tootap/Track-on-track/firmware/msp430fr6989.h

/* ============================================================================ */
/* Copyright (c) 2017, Texas Instruments Incorporated                           */
/*  All rights reserved.                                                        */
/*                                                                              */
/*  Redistribution and use in source and binary forms, with or without          */
/*  modification, are permitted provided that the following conditions          */
/*  are met:                                                                    */
/*                                                                              */
/*  *  Redistributions of source code must retain the above copyright           */
/*     notice, this list of conditions and the following disclaimer.            */
/*                                                                              */
/*  *  Redistributions in binary form must reproduce the above copyright        */
/*     notice, this list of conditions and the following disclaimer in the      */
/*     documentation and/or other materials provided with the distribution.     */
/*                                                                              */
/*  *  Neither the name of Texas Instruments Incorporated nor the names of      */
/*     its contributors may be used to endorse or promote products derived      */
/*     from this software without specific prior written permission.            */
/*                                                                              */
/*  THIS SOFTWARE IS PROVIDED BY THE COPYRIGHT HOLDERS AND CONTRIBUTORS "AS IS" */
/*  AND ANY EXPRESS OR IMPLIED WARRANTIES, INCLUDING, BUT NOT LIMITED TO,       */
/*  THE IMPLIED WARRANTIES OF MERCHANTABILITY AND FITNESS FOR A PARTICULAR      */
/*  PURPOSE ARE DISCLAIMED. IN NO EVENT SHALL THE COPYRIGHT OWNER OR            */
/*  CONTRIBUTORS BE LIABLE FOR ANY DIRECT, INDIRECT, INCIDENTAL, SPECIAL,       */
/*  EXEMPLARY, OR CONSEQUENTIAL DAMAGES (INCLUDING, BUT NOT LIMITED TO,         */
/*  PROCUREMENT OF SUBSTITUTE GOODS OR SERVICES; LOSS OF USE, DATA, OR PROFITS; */
/*  OR BUSINESS INTERRUPTION) HOWEVER CAUSED AND ON ANY THEORY OF LIABILITY,    */
/*  WHETHER IN CONTRACT, STRICT LIABILITY, OR TORT (INCLUDING NEGLIGENCE OR     */
/*  OTHERWISE) ARISING IN ANY WAY OUT OF THE USE OF THIS SOFTWARE,              */
/*  EVEN IF ADVISED OF THE POSSIBILITY OF SUCH DAMAGE.                          */
/* ============================================================================ */

/********************************************************************
*
* Standard register and bit definitions for the Texas Instruments
* MSP430 microcontroller.
*
* This file supports assembler and C development for
* MSP430FR6989 devices.
*
* Texas Instruments, Version 1.1
*
* Rev. 1.0, Setup
* Rev. 1.1, ESI: Renamed bit ESIVCC2 to ESIVMIDEN, renamed bit ESIVSS to ESISHTSM
*
*
********************************************************************/

#ifndef __MSP430FR6989
#define __MSP430FR6989

#define __MSP430_HAS_MSP430XV2_CPU__                /* Definition to show that it has MSP430XV2 CPU */
#define __MSP430FR5XX_6XX_FAMILY__

#define __MSP430_HEADER_VERSION__ 1203

#ifdef __cplusplus
extern "C" {
#endif


/*----------------------------------------------------------------------------*/
/* PERIPHERAL FILE MAP                                                        */
/*----------------------------------------------------------------------------*/

#ifndef SFR_8BIT
/* External references resolved by a device-specific linker command file */
#define SFR_8BIT(address)   extern volatile unsigned char address
#define SFR_16BIT(address)  extern volatile unsigned int address
//#define SFR_20BIT(address)  extern volatile unsigned int address
typedef void (* __SFR_FARPTR)();
#define SFR_20BIT(address) extern __SFR_FARPTR address
#define SFR_32BIT(address)  extern volatile unsigned long address

#endif


/************************************************************
* STANDARD BITS
************************************************************/

#define BIT0                   (0x0001)
#define BIT1                   (0x0002)
#define BIT2                   (0x0004)
#define BIT3                   (0x0008)
#define BIT4                   (0x0010)
#define BIT5                   (0x0020)
#define BIT6                   (0x0040)
#define BIT7                   (0x0080)
#define BIT8                   (0x0100)
#define BIT9                   (0x0200)
#define BITA                   (0x0400)
#define BITB                   (0x0800)
#define BITC                   (0x1000)
#define BITD                   (0x2000)
#define BITE                   (0x4000)
#define BITF                   (0x8000)

/************************************************************
* STATUS REGISTER BITS
************************************************************/

#define C                      (0x0001)
#define Z                      (0x0002)
#define N                      (0x0004)
#define V                      (0x0100)
#define GIE                    (0x0008)
#define CPUOFF                 (0x0010)
#define OSCOFF                 (0x0020)
#define SCG0                   (0x0040)
#define SCG1                   (0x0080)

/* Low Power Modes coded with Bits 4-7 in SR */

#ifdef __ASM_HEADER__ /* Begin #defines for assembler */
#define LPM0                   (CPUOFF)
#define LPM1                   (SCG0+CPUOFF)
#define LPM2                   (SCG1+CPUOFF)
#define LPM3                   (SCG1+SCG0+CPUOFF)
#define LPM4                   (SCG1+SCG0+OSCOFF+CPUOFF)
/* End #defines for assembler */

#else /* Begin #defines for C */
#define LPM0_bits              (CPUOFF)
#define LPM1_bits              (SCG0+CPUOFF)
#define LPM2_bits              (SCG1+CPUOFF)
#define LPM3_bits              (SCG1+SCG0+CPUOFF)
#define LPM4_bits              (SCG1+SCG0+OSCOFF+CPUOFF)

#include "in430.h"
#include <intrinsics.h>

#define LPM0      __bis_SR_register(LPM0_bits)         /* Enter Low Power Mode 0 */
#define LPM0_EXIT __bic_SR_register_on_exit(LPM0_bits) /* Exit Low Power Mode 0 */
#define LPM1      __bis_SR_register(LPM1_bits)         /* Enter Low Power Mode 1 */
#define LPM1_EXIT __bic_SR_register_on_exit(LPM1_bits) /* Exit Low Power Mode 1 */
#define LPM2      __bis_SR_register(LPM2_bits)         /* Enter Low Power Mode 2 */
#define LPM2_EXIT __bic_SR_register_on_exit(LPM2_bits) /* Exit Low Power Mode 2 */
#define LPM3      __bis_SR_register(LPM3_bits)         /* Enter Low Power Mode 3 */
#define LPM3_EXIT __bic_SR_register_on_exit(LPM3_bits) /* Exit Low Power Mode 3 */
#define LPM4      __bis_SR_register(LPM4_bits)         /* Enter Low Power Mode 4 */
#define LPM4_EXIT __bic_SR_register_on_exit(LPM4_bits) /* Exit Low Power Mode 4 */
#endif /* End #defines for C */

/************************************************************
* PERIPHERAL FILE MAP
************************************************************/

/************************************************************
* ADC12_B
************************************************************/
#define __MSP430_HAS_ADC12_B__                /* Definition to show that Module is available */
#define __MSP430_BASEADDRESS_ADC12_B__ 0x0800
#define ADC12_B_BASE           __MSP430_BASEADDRESS_ADC12_B__

SFR_16BIT(ADC12CTL0);                         /* ADC12 B Control 0 */
SFR_8BIT(ADC12CTL0_L);                        /* ADC12 B Control 0 */
SFR_8BIT(ADC12CTL0_H);                        /* ADC12 B Control 0 */
SFR_16BIT(ADC12CTL1);                         /* ADC12 B Control 1 */
SFR_8BIT(ADC12CTL1_L);                        /* ADC12 B Control 1 */
SFR_8BIT(ADC12CTL1_H);                        /* ADC12 B Control 1 */
SFR_16BIT(ADC12CTL2);                         /* ADC12 B Control 2 */
SFR_8BIT(ADC12CTL2_L);                        /* ADC12 B Control 2 */
SFR_8BIT(ADC12CTL2_H);                        /* ADC12 B Control 2 */
SFR_16BIT(ADC12CTL3);                         /* ADC12 B Control 3 */
SFR_8BIT(ADC12CTL3_L);                        /* ADC12 B Control 3 */
SFR_8BIT(ADC12CTL3_H);                        /* ADC12 B Control 3 */
SFR_16BIT(ADC12LO);                           /* ADC12 B Window Comparator High Threshold */
SFR_8BIT(ADC12LO_L);                          /* ADC12 B Window Comparator High Threshold */
SFR_8BIT(ADC12LO_H);                          /* ADC12 B Window Comparator High Threshold */
SFR_16BIT(ADC12HI);                           /* ADC12 B Window Comparator High Threshold */
SFR_8BIT(ADC12HI_L);                          /* ADC12 B Window Comparator High Threshold */
SFR_8BIT(ADC12HI_H);                          /* ADC12 B Window Comparator High Threshold */
SFR_16BIT(ADC12IFGR0);                        /* ADC12 B Interrupt Flag 0 */
SFR_8BIT(ADC12IFGR0_L);                       /* ADC12 B Interrupt Flag 0 */
SFR_8BIT(ADC12IFGR0_H);                       /* ADC12 B Interrupt Flag 0 */
SFR_16BIT(ADC12IFGR1);                        /* ADC12 B Interrupt Flag 1 */
SFR_8BIT(ADC12IFGR1_L);                       /* ADC12 B Interrupt Flag 1 */
SFR_8BIT(ADC12IFGR1_H);                       /* ADC12 B Interrupt Flag 1 */
SFR_16BIT(ADC12IFGR2);                        /* ADC12 B Interrupt Flag 2 */
SFR_8BIT(ADC12IFGR2_L);                       /* ADC12 B Interrupt Flag 2 */
SFR_8BIT(ADC12IFGR2_H);                       /* ADC12 B Interrupt Flag 2 */
SFR_16BIT(ADC12IER0);                         /* ADC12 B Interrupt Enable 0 */
SFR_8BIT(ADC12IER0_L);                        /* ADC12 B Interrupt Enable 0 */
SFR_8BIT(ADC12IER0_H);                        /* ADC12 B Interrupt Enable 0 */
SFR_16BIT(ADC12IER1);                         /* ADC12 B Interrupt Enable 1 */
SFR_8BIT(ADC12IER1_L);                        /* ADC12 B Interrupt Enable 1 */
SFR_8BIT(ADC12IER1_H);                        /* ADC12 B Interrupt Enable 1 */
SFR_16BIT(ADC12IER2);                         /* ADC12 B Interrupt Enable 2 */
SFR_8BIT(ADC12IER2_L);                        /* ADC12 B Interrupt Enable 2 */
SFR_8BIT(ADC12IER2_H);                        /* ADC12 B Interrupt Enable 2 */
SFR_16BIT(ADC12IV);                           /* ADC12 B Interrupt Vector Word */
SFR_8BIT(ADC12IV_L);                          /* ADC12 B Interrupt Vector Word */
SFR_8BIT(ADC12IV_H);                          /* ADC12 B Interrupt Vector Word */

SFR_16BIT(ADC12MCTL0);                        /* ADC12 Memory Control 0 */
SFR_8BIT(ADC12MCTL0_L);                       /* ADC12 Memory Control 0 */
SFR_8BIT(ADC12MCTL0_H);                       /* ADC12 Memory Control 0 */
SFR_16BIT(ADC12MCTL1);                        /* ADC12 Memory Control 1 */
SFR_8BIT(ADC12MCTL1_L);                       /* ADC12 Memory Control 1 */
SFR_8BIT(ADC12MCTL1_H);                       /* ADC12 Memory Control 1 */
SFR_16BIT(ADC12MCTL2);                        /* ADC12 Memory Control 2 */
SFR_8BIT(ADC12MCTL2_L);                       /* ADC12 Memory Control 2 */
SFR_8BIT(ADC12MCTL2_H);                       /* ADC12 Memory Control 2 */
SFR_16BIT(ADC12MCTL3);                        /* ADC12 Memory Control 3 */
SFR_8BIT(ADC12MCTL3_L);                       /* ADC12 Memory Control 3 */
SFR_8BIT(ADC12MCTL3_H);                       /* ADC12 Memory Control 3 */
SFR_16BIT(ADC12MCTL4);                        /* ADC12 Memory Control 4 */
SFR_8BIT(ADC12MCTL4_L);                       /* ADC12 Memory Control 4 */
SFR_8BIT(ADC12MCTL4_H);                       /* ADC12 Memory Control 4 */
SFR_16BIT(ADC12MCTL5);                        /* ADC12 Memory Control 5 */
SFR_8BIT(ADC12MCTL5_L);                       /* ADC12 Memory Control 5 */
SFR_8BIT(ADC12MCTL5_H);                       /* ADC12 Memory Control 5 */
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
SFR_8BIT(ADC12MCTL24_H);                      /* ADC12 Memory Control 24 */
SFR_16BIT(ADC12MCTL25);                       /* ADC12 Memory Control 25 */
SFR_8BIT(ADC12MCTL25_L);                      /* ADC12 Memory Control 25 */
SFR_8BIT(ADC12MCTL25_H);                      /* ADC12 Memory Control 25 */
SFR_16BIT(ADC12MCTL26);                       /* ADC12 Memory Control 26 */
SFR_8BIT(ADC12MCTL26_L);                      /* ADC12 Memory Control 26 */
SFR_8BIT(ADC12MCTL26_H);                      /* ADC12 Memory Control 26 */
SFR_16BIT(ADC12MCTL27);                       /* ADC12 Memory Control 27 */
SFR_8BIT(ADC12MCTL27_L);                      /* ADC12 Memory Control 27 */
SFR_8BIT(ADC12MCTL27_H);                      /* ADC12 Memory Control 27 */
SFR_16BIT(ADC12MCTL28);                       /* ADC12 Memory Control 28 */
SFR_8BIT(ADC12MCTL28_L);                      /* ADC12 Memory Control 28 */
SFR_8BIT(ADC12MCTL28_H);                      /* ADC12 Memory Control 28 */
SFR_16BIT(ADC12MCTL29);                       /* ADC12 Memory Control 29 */
SFR_8BIT(ADC12MCTL29_L);                      /* ADC12 Memory Control 29 */
SFR_8BIT(ADC12MCTL29_H);                      /* ADC12 Memory Control 29 */
SFR_16BIT(ADC12MCTL30);                       /* ADC12 Memory Control 30 */
SFR_8BIT(ADC12MCTL30_L);                      /* ADC12 Memory Control 30 */
SFR_8BIT(ADC12MCTL30_H);                      /* ADC12 Memory Control 30 */
SFR_16BIT(ADC12MCTL31);                       /* ADC12 Memory Control 31 */
SFR_8BIT(ADC12MCTL31_L);                      /* ADC12 Memory Control 31 */
SFR_8BIT(ADC12MCTL31_H);                      /* ADC12 Memory Control 31 */
#define ADC12MCTL_             ADC12MCTL      /* ADC12 Memory Control */
#ifdef __ASM_HEADER__
#define ADC12MCTL              ADC12MCTL0     /* ADC12 Memory Control (for assembler) */
#else
#define ADC12MCTL              ((char*)       &ADC12MCTL0) /* ADC12 Memory Control (for C) */
#endif

SFR_16BIT(ADC12MEM0);                         /* ADC12 Conversion Memory 0 */
SFR_8BIT(ADC12MEM0_L);                        /* ADC12 Conversion Memory 0 */
SFR_8BIT(ADC12MEM0_H);                        /* ADC12 Conversion Memory 0 */
SFR_16BIT(ADC12MEM1);                         /* ADC12 Conversion Memory 1 */
SFR_8BIT(ADC12MEM1_L);                        /* ADC12 Conversion Memory 1 */
SFR_8BIT(ADC12MEM1_H);                        /* ADC12 Conversion Memory 1 */
SFR_16BIT(ADC12MEM2);                         /* ADC12 Conversion Memory 2 */
SFR_8BIT(ADC12MEM2_L);                        /* ADC12 Conversion Memory 2 */
SFR_8BIT(ADC12MEM2_H);                        /* ADC12 Conversion Memory 2 */
SFR_16BIT(ADC12MEM3);                         /* ADC12 Conversion Memory 3 */
SFR_8BIT(ADC12MEM3_L);                        /* ADC12 Conversion Memory 3 */
SFR_8BIT(ADC12MEM3_H);                        /* ADC12 Conversion Memory 3 */
SFR_16BIT(ADC12MEM4);                         /* ADC12 Conversion Memory 4 */
SFR_8BIT(ADC12MEM4_L);                        /* ADC12 Conversion Memory 4 */
SFR_8BIT(ADC12MEM4_H);                        /* ADC12 Conversion Memory 4 */
SFR_16BIT(ADC12MEM5);                         /* ADC12 Conversion Memory 5 */
SFR_8BIT(ADC12MEM5_L);                        /* ADC12 Conversion Memory 5 */
SFR_8BIT(ADC12MEM5_H);                        /* ADC12 Conversion Memory 5 */
SFR_16BIT(ADC12MEM6);                         /* ADC12 Conversion Memory 6 */
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
SFR_16BIT(ADC12MEM24);                        /* ADC12 Conversion Memory 24 */
SFR_8BIT(ADC12MEM24_L);                       /* ADC12 Conversion Memory 24 */
SFR_8BIT(ADC12MEM24_H);                       /* ADC12 Conversion Memory 24 */
SFR_16BIT(ADC12MEM25);                        /* ADC12 Conversion Memory 25 */
SFR_8BIT(ADC12MEM25_L);                       /* ADC12 Conversion Memory 25 */
SFR_8BIT(ADC12MEM25_H);                       /* ADC12 Conversion Memory 25 */
SFR_16BIT(ADC12MEM26);                        /* ADC12 Conversion Memory 26 */
SFR_8BIT(ADC12MEM26_L);                       /* ADC12 Conversion Memory 26 */
SFR_8BIT(ADC12MEM26_H);                       /* ADC12 Conversion Memory 26 */
SFR_16BIT(ADC12MEM27);                        /* ADC12 Conversion Memory 27 */
SFR_8BIT(ADC12MEM27_L);                       /* ADC12 Conversion Memory 27 */
SFR_8BIT(ADC12MEM27_H);                       /* ADC12 Conversion Memory 27 */
SFR_16BIT(ADC12MEM28);                        /* ADC12 Conversion Memory 28 */
SFR_8BIT(ADC12MEM28_L);                       /* ADC12 Conversion Memory 28 */
SFR_8BIT(ADC12MEM28_H);                       /* ADC12 Conversion Memory 28 */
SFR_16BIT(ADC12MEM29);                        /* ADC12 Conversion Memory 29 */
SFR_8BIT(ADC12MEM29_L);                       /* ADC12 Conversion Memory 29 */
SFR_8BIT(ADC12MEM29_H);                       /* ADC12 Conversion Memory 29 */
SFR_16BIT(ADC12MEM30);                        /* ADC12 Conversion Memory 30 */
SFR_8BIT(ADC12MEM30_L);                       /* ADC12 Conversion Memory 30 */
SFR_8BIT(ADC12MEM30_H);                       /* ADC12 Conversion Memory 30 */
SFR_16BIT(ADC12MEM31);                        /* ADC12 Conversion Memory 31 */
SFR_8BIT(ADC12MEM31_L);                       /* ADC12 Conversion Memory 31 */
SFR_8BIT(ADC12MEM31_H);                       /* ADC12 Conversion Memory 31 */
#define ADC12MEM_              ADC12MEM       /* ADC12 Conversion Memory */
#ifdef __ASM_HEADER__
#define ADC12MEM               ADC12MEM0      /* ADC12 Conversion Memory (for assembler) */
#else
#define ADC12MEM               ((int*)        &ADC12MEM0) /* ADC12 Conversion Memory (for C) */
#endif

/* ADC12CTL0 Control Bits */
#define ADC12SC                (0x0001)       /* ADC12 Start Conversion */
#define ADC12ENC               (0x0002)       /* ADC12 Enable Conversion */
#define ADC12ON                (0x0010)       /* ADC12 On/enable */
#define ADC12MSC               (0x0080)       /* ADC12 Multiple SampleConversion */
#define ADC12SHT00             (0x0100)       /* ADC12 Sample Hold 0 Select Bit: 0 */
#define ADC12SHT01             (0x0200)       /* ADC12 Sample Hold 0 Select Bit: 1 */
#define ADC12SHT02             (0x0400)       /* ADC12 Sample Hold 0 Select Bit: 2 */
#define ADC12SHT03             (0x0800)       /* ADC12 Sample Hold 0 Select Bit: 3 */
#define ADC12SHT10             (0x1000)       /* ADC12 Sample Hold 1 Select Bit: 0 */
#define ADC12SHT11             (0x2000)       /* ADC12 Sample Hold 1 Select Bit: 1 */
#define ADC12SHT12             (0x4000)       /* ADC12 Sample Hold 1 Select Bit: 2 */
#define ADC12SHT13             (0x8000)       /* ADC12 Sample Hold 1 Select Bit: 3 */

/* ADC12CTL0 Control Bits */
#define ADC12SC_L              (0x0001)       /* ADC12 Start Conversion */
#define ADC12ENC_L             (0x0002)       /* ADC12 Enable Conversion */
#define ADC12ON_L              (0x0010)       /* ADC12 On/enable */
#define ADC12MSC_L             (0x0080)       /* ADC12 Multiple SampleConversion */

/* ADC12CTL0 Control Bits */
#define ADC12SHT00_H           (0x0001)       /* ADC12 Sample Hold 0 Select Bit: 0 */
#define ADC12SHT01_H           (0x0002)       /* ADC12 Sample Hold 0 Select Bit: 1 */
#define ADC12SHT02_H           (0x0004)       /* ADC12 Sample Hold 0 Select Bit: 2 */
#define ADC12SHT03_H           (0x0008)       /* ADC12 Sample Hold 0 Select Bit: 3 */
#define ADC12SHT10_H           (0x0010)       /* ADC12 Sample Hold 1 Select Bit: 0 */
#define ADC12SHT11_H           (0x0020)       /* ADC12 Sample Hold 1 Select Bit: 1 */
#define ADC12SHT12_H           (0x0040)       /* ADC12 Sample Hold 1 Select Bit: 2 */
#define ADC12SHT13_H           (0x0080)       /* ADC12 Sample Hold 1 Select Bit: 3 */

#define ADC12SHT0_0            (0*0x100u)     /* ADC12 Sample Hold 0 Select Bit: 0 */
#define ADC12SHT0_1            (1*0x100u)     /* ADC12 Sample Hold 0 Select Bit: 1 */
#define ADC12SHT0_2            (2*0x100u)     /* ADC12 Sample Hold 0 Select Bit: 2 */
#define ADC12SHT0_3            (3*0x100u)     /* ADC12 Sample Hold 0 Select Bit: 3 */
#define ADC12SHT0_4            (4*0x100u)     /* ADC12 Sample Hold 0 Select Bit: 4 */
#define ADC12SHT0_5            (5*0x100u)     /* ADC12 Sample Hold 0 Select Bit: 5 */
#define ADC12SHT0_6            (6*0x100u)     /* ADC12 Sample Hold 0 Select Bit: 6 */
#define ADC12SHT0_7            (7*0x100u)     /* ADC12 Sample Hold 0 Select Bit: 7 */
#define ADC12SHT0_8            (8*0x100u)     /* ADC12 Sample Hold 0 Select Bit: 8 */
#define ADC12SHT0_9            (9*0x100u)     /* ADC12 Sample Hold 0 Select Bit: 9 */
#define ADC12SHT0_10           (10*0x100u)    /* ADC12 Sample Hold 0 Select Bit: 10 */
#define ADC12SHT0_11           (11*0x100u)    /* ADC12 Sample Hold 0 Select Bit: 11 */
#define ADC12SHT0_12           (12*0x100u)    /* ADC12 Sample Hold 0 Select Bit: 12 */
#define ADC12SHT0_13           (13*0x100u)    /* ADC12 Sample Hold 0 Select Bit: 13 */
#define ADC12SHT0_14           (14*0x100u)    /* ADC12 Sample Hold 0 Select Bit: 14 */
#define ADC12SHT0_15           (15*0x100u)    /* ADC12 Sample Hold 0 Select Bit: 15 */

#define ADC12SHT1_0            (0*0x1000u)    /* ADC12 Sample Hold 1 Select Bit: 0 */
#define ADC12SHT1_1            (1*0x1000u)    /* ADC12 Sample Hold 1 Select Bit: 1 */
#define ADC12SHT1_2            (2*0x1000u)    /* ADC12 Sample Hold 1 Select Bit: 2 */
#define ADC12SHT1_3            (3*0x1000u)    /* ADC12 Sample Hold 1 Select Bit: 3 */
#define ADC12SHT1_4            (4*0x1000u)    /* ADC12 Sample Hold 1 Select Bit: 4 */
#define ADC12SHT1_5            (5*0x1000u)    /* ADC12 Sample Hold 1 Select Bit: 5 */
#define ADC12SHT1_6            (6*0x1000u)    /* ADC12 Sample Hold 1 Select Bit: 6 */
#define ADC12SHT1_7            (7*0x1000u)    /* ADC12 Sample Hold 1 Select Bit: 7 */
#define ADC12SHT1_8            (8*0x1000u)    /* ADC12 Sample Hold 1 Select Bit: 8 */
#define ADC12SHT1_9            (9*0x1000u)    /* ADC12 Sample Hold 1 Select Bit: 9 */
#define ADC12SHT1_10           (10*0x1000u)   /* ADC12 Sample Hold 1 Select Bit: 10 */
#define ADC12SHT1_11           (11*0x1000u)   /* ADC12 Sample Hold 1 Select Bit: 11 */
#define ADC12SHT1_12           (12*0x1000u)   /* ADC12 Sample Hold 1 Select Bit: 12 */
#define ADC12SHT1_13           (13*0x1000u)   /* ADC12 Sample Hold 1 Select Bit: 13 */
#define ADC12SHT1_14           (14*0x1000u)   /* ADC12 Sample Hold 1 Select Bit: 14 */
#define ADC12SHT1_15           (15*0x1000u)   /* ADC12 Sample Hold 1 Select Bit: 15 */

/* ADC12CTL1 Control Bits */
#define ADC12BUSY              (0x0001)       /* ADC12 Busy */
#define ADC12CONSEQ0           (0x0002)       /* ADC12 Conversion Sequence Select Bit: 0 */
#define ADC12CONSEQ1           (0x0004)       /* ADC12 Conversion Sequence Select Bit: 1 */
#define ADC12SSEL0             (0x0008)       /* ADC12 Clock Source Select Bit: 0 */
#define ADC12SSEL1             (0x0010)       /* ADC12 Clock Source Select Bit: 1 */
#define ADC12DIV0              (0x0020)       /* ADC12 Clock Divider Select Bit: 0 */
#define ADC12DIV1              (0x0040)       /* ADC12 Clock Divider Select Bit: 1 */
#define ADC12DIV2              (0x0080)       /* ADC12 Clock Divider Select Bit: 2 */
#define ADC12ISSH              (0x0100)       /* ADC12 Invert Sample Hold Signal */
#define ADC12SHP               (0x0200)       /* ADC12 Sample/Hold Pulse Mode */
#define ADC12SHS0              (0x0400)       /* ADC12 Sample/Hold Source Bit: 0 */
#define ADC12SHS1              (0x0800)       /* ADC12 Sample/Hold Source Bit: 1 */
#define ADC12SHS2              (0x1000)       /* ADC12 Sample/Hold Source Bit: 2 */
#define ADC12PDIV0             (0x2000)       /* ADC12 Predivider Bit: 0 */
#define ADC12PDIV1             (0x4000)       /* ADC12 Predivider Bit: 1 */

/* ADC12CTL1 Control Bits */
#define ADC12BUSY_L            (0x0001)       /* ADC12 Busy */
#define ADC12CONSEQ0_L         (0x0002)       /* ADC12 Conversion Sequence Select Bit: 0 */
#define ADC12CONSEQ1_L         (0x0004)       /* ADC12 Conversion Sequence Select Bit: 1 */
#define ADC12SSEL0_L           (0x0008)       /* ADC12 Clock Source Select Bit: 0 */
#define ADC12SSEL1_L           (0x0010)       /* ADC12 Clock Source Select Bit: 1 */
#define ADC12DIV0_L            (0x0020)       /* ADC12 Clock Divider Select Bit: 0 */
#define ADC12DIV1_L            (0x0040)       /* ADC12 Clock Divider Select Bit: 1 */
#define ADC12DIV2_L            (0x0080)       /* ADC12 Clock Divider Select Bit: 2 */

/* ADC12CTL1 Control Bits */
#define ADC12ISSH_H            (0x0001)       /* ADC12 Invert Sample Hold Signal */
#define ADC12SHP_H             (0x0002)       /* ADC12 Sample/Hold Pulse Mode */
#define ADC12SHS0_H            (0x0004)       /* ADC12 Sample/Hold Source Bit: 0 */
#define ADC12SHS1_H            (0x0008)       /* ADC12 Sample/Hold Source Bit: 1 */
#define ADC12SHS2_H            (0x0010)       /* ADC12 Sample/Hold Source Bit: 2 */
#define ADC12PDIV0_H           (0x0020)       /* ADC12 Predivider Bit: 0 */
#define ADC12PDIV1_H           (0x0040)       /* ADC12 Predivider Bit: 1 */

#define ADC12CONSEQ_0          (0*0x0002u)    /* ADC12 Conversion Sequence Select: 0 */
#define ADC12CONSEQ_1          (1*0x0002u)    /* ADC12 Conversion Sequence Select: 1 */
#define ADC12CONSEQ_2          (2*0x0002u)    /* ADC12 Conversion Sequence Select: 2 */
#define ADC12CONSEQ_3          (3*0x0002u)    /* ADC12 Conversion Sequence Select: 3 */

#define ADC12SSEL_0            (0*0x0008u)    /* ADC12 Clock Source Select: 0 */
#define ADC12SSEL_1            (1*0x0008u)    /* ADC12 Clock Source Select: 1 */
#define ADC12SSEL_2            (2*0x0008u)    /* ADC12 Clock Source Select: 2 */
#define ADC12SSEL_3            (3*0x0008u)    /* ADC12 Clock Source Select: 3 */

#define ADC12DIV_0             (0*0x0020u)    /* ADC12 Clock Divider Select: 0 */
#define ADC12DIV_1             (1*0x0020u)    /* ADC12 Clock Divider Select: 1 */
#define ADC12DIV_2             (2*0x0020u)    /* ADC12 Clock Divider Select: 2 */
#define ADC12DIV_3             (3*0x0020u)    /* ADC12 Clock Divider Select: 3 */
#define ADC12DIV_4             (4*0x0020u)    /* ADC12 Clock Divider Select: 4 */
#define ADC12DIV_5             (5*0x0020u)    /* ADC12 Clock Divider Select: 5 */
#define ADC12DIV_6             (6*0x0020u)    /* ADC12 Clock Divider Select: 6 */
#define ADC12DIV_7             (7*0x0020u)    /* ADC12 Clock Divider Select: 7 */

#define ADC12SHS_0             (0*0x0400u)    /* ADC12 Sample/Hold Source: 0 */
#define ADC12SHS_1             (1*0x0400u)    /* ADC12 Sample/Hold Source: 1 */
#define ADC12SHS_2             (2*0x0400u)    /* ADC12 Sample/Hold Source: 2 */
#define ADC12SHS_3             (3*0x0400u)    /* ADC12 Sample/Hold Source: 3 */
#define ADC12SHS_4             (4*0x0400u)    /* ADC12 Sample/Hold Source: 4 */
#define ADC12SHS_5             (5*0x0400u)    /* ADC12 Sample/Hold Source: 5 */
#define ADC12SHS_6             (6*0x0400u)    /* ADC12 Sample/Hold Source: 6 */
#define ADC12SHS_7             (7*0x0400u)    /* ADC12 Sample/Hold Source: 7 */

#define ADC12PDIV_0            (0*0x2000u)    /* ADC12 Clock predivider Select 0 */
#define ADC12PDIV_1            (1*0x2000u)    /* ADC12 Clock predivider Select 1 */
#define ADC12PDIV_2            (2*0x2000u)    /* ADC12 Clock predivider Select 2 */
#define ADC12PDIV_3            (3*0x2000u)    /* ADC12 Clock predivider Select 3 */
#define ADC12PDIV__1           (0*0x2000u)    /* ADC12 Clock predivider Select: /1 */
#define ADC12PDIV__4           (1*0x2000u)    /* ADC12 Clock predivider Select: /4 */
#define ADC12PDIV__32          (2*0x2000u)    /* ADC12 Clock predivider Select: /32 */
#define ADC12PDIV__64          (3*0x2000u)    /* ADC12 Clock predivider Select: /64 */

/* ADC12CTL2 Control Bits */
#define ADC12PWRMD             (0x0001)       /* ADC12 Power Mode */
#define ADC12DF                (0x0008)       /* ADC12 Data Format */
#define ADC12RES0              (0x0010)       /* ADC12 Resolution Bit: 0 */
#define ADC12RES1              (0x0020)       /* ADC12 Resolution Bit: 1 */

/* ADC12CTL2 Control Bits */
#define ADC12PWRMD_L           (0x0001)       /* ADC12 Power Mode */
#define ADC12DF_L              (0x0008)       /* ADC12 Data Format */
#define ADC12RES0_L            (0x0010)       /* ADC12 Resolution Bit: 0 */
#define ADC12RES1_L            (0x0020)       /* ADC12 Resolution Bit: 1 */

#define ADC12RES_0             (0x0000)       /* ADC12+ Resolution : 8 Bit */
#define ADC12RES_1             (0x0010)       /* ADC12+ Resolution : 10 Bit */
#define ADC12RES_2             (0x0020)       /* ADC12+ Resolution : 12 Bit */
#define ADC12RES_3             (0x0030)       /* ADC12+ Resolution : reserved */

#define ADC12RES__8BIT         (0x0000)       /* ADC12+ Resolution : 8 Bit */
#define ADC12RES__10BIT        (0x0010)       /* ADC12+ Resolution : 10 Bit */
#define ADC12RES__12BIT        (0x0020)       /* ADC12+ Resolution : 12 Bit */

/* ADC12CTL3 Control Bits */
#define ADC12CSTARTADD0        (0x0001)       /* ADC12 Conversion Start Address Bit: 0 */
#define ADC12CSTARTADD1        (0x0002)       /* ADC12 Conversion Start Address Bit: 1 */
#define ADC12CSTARTADD2        (0x0004)       /* ADC12 Conversion Start Address Bit: 2 */
#define ADC12CSTARTADD3        (0x0008)       /* ADC12 Conversion Start Address Bit: 3 */
#define ADC12CSTARTADD4        (0x0010)       /* ADC12 Conversion Start Address Bit: 4 */
#define ADC12BATMAP            (0x0040)       /* ADC12 Internal AVCC/2 select */
#define ADC12TCMAP             (0x0080)       /* ADC12 Internal TempSensor select */
#define ADC12ICH0MAP           (0x0100)       /* ADC12 Internal Channel 0 select */
#define ADC12ICH1MAP           (0x0200)       /* ADC12 Internal Channel 1 select */
#define ADC12ICH2MAP           (0x0400)       /* ADC12 Internal Channel 2 select */
#define ADC12ICH3MAP           (0x0800)       /* ADC12 Internal Channel 3 select */

/* ADC12CTL3 Control Bits */
#define ADC12CSTARTADD0_L      (0x0001)       /* ADC12 Conversion Start Address Bit: 0 */
#define ADC12CSTARTADD1_L      (0x0002)       /* ADC12 Conversion Start Address Bit: 1 */
#define ADC12CSTARTADD2_L      (0x0004)       /* ADC12 Conversion Start Address Bit: 2 */
#define ADC12CSTARTADD3_L      (0x0008)       /* ADC12 Conversion Start Address Bit: 3 */
#define ADC12CSTARTADD4_L      (0x0010)       /* ADC12 Conversion Start Address Bit: 4 */
#define ADC12BATMAP_L          (0x0040)       /* ADC12 Internal AVCC/2 select */
#define ADC12TCMAP_L           (0x0080)       /* ADC12 Internal TempSensor select */

/* ADC12CTL3 Control Bits */
#define ADC12ICH0MAP_H         (0x0001)       /* ADC12 Internal Channel 0 select */
#define ADC12ICH1MAP_H         (0x0002)       /* ADC12 Internal Channel 1 select */
#define ADC12ICH2MAP_H         (0x0004)       /* ADC12 Internal Channel 2 select */
#define ADC12ICH3MAP_H         (0x0008)       /* ADC12 Internal Channel 3 select */

#define ADC12CSTARTADD_0       (              0*0x0001u) /* ADC12 Conversion Start Address: 0 */
#define ADC12CSTARTADD_1       (              1*0x0001u) /* ADC12 Conversion Start Address: 1 */
#define ADC12CSTARTADD_2       (              2*0x0001u) /* ADC12 Conversion Start Address: 2 */
#define ADC12CSTARTADD_3       (              3*0x0001u) /* ADC12 Conversion Start Address: 3 */
#define ADC12CSTARTADD_4       (              4*0x0001u) /* ADC12 Conversion Start Address: 4 */
#define ADC12CSTARTADD_5       (              5*0x0001u) /* ADC12 Conversion Start Address: 5 */
#define ADC12CSTARTADD_6       (              6*0x0001u) /* ADC12 Conversion Start Address: 6 */
#define ADC12CSTARTADD_7       (              7*0x0001u) /* ADC12 Conversion Start Address: 7 */
#define ADC12CSTARTADD_8       (              8*0x0001u) /* ADC12 Conversion Start Address: 8 */
#define ADC12CSTARTADD_9       (              9*0x0001u) /* ADC12 Conversion Start Address: 9 */
#define ADC12CSTARTADD_10      (10*0x0001u)   /* ADC12 Conversion Start Address: 10 */
#define ADC12CSTARTADD_11      (11*0x0001u)   /* ADC12 Conversion Start Address: 11 */
#define ADC12CSTARTADD_12      (12*0x0001u)   /* ADC12 Conversion Start Address: 12 */
#define ADC12CSTARTADD_13      (13*0x0001u)   /* ADC12 Conversion Start Address: 13 */
#define ADC12CSTARTADD_14      (14*0x0001u)   /* ADC12 Conversion Start Address: 14 */
#define ADC12CSTARTADD_15      (15*0x0001u)   /* ADC12 Conversion Start Address: 15 */
#define ADC12CSTARTADD_16      (16*0x0001u)   /* ADC12 Conversion Start Address: 16 */
#define ADC12CSTARTADD_17      (17*0x0001u)   /* ADC12 Conversion Start Address: 17 */
#define ADC12CSTARTADD_18      (18*0x0001u)   /* ADC12 Conversion Start Address: 18 */
#define ADC12CSTARTADD_19      (19*0x0001u)   /* ADC12 Conversion Start Address: 19 */
#define ADC12CSTARTADD_20      (20*0x0001u)   /* ADC12 Conversion Start Address: 20 */
#define ADC12CSTARTADD_21      (21*0x0001u)   /* ADC12 Conversion Start Address: 21 */
#define ADC12CSTARTADD_22      (22*0x0001u)   /* ADC12 Conversion Start Address: 22 */
#define ADC12CSTARTADD_23      (23*0x0001u)   /* ADC12 Conversion Start Address: 23 */
#define ADC12CSTARTADD_24      (24*0x0001u)   /* ADC12 Conversion Start Address: 24 */
#define ADC12CSTARTADD_25      (25*0x0001u)   /* ADC12 Conversion Start Address: 25 */
#define ADC12CSTARTADD_26      (26*0x0001u)   /* ADC12 Conversion Start Address: 26 */
#define ADC12CSTARTADD_27      (27*0x0001u)   /* ADC12 Conversion Start Address: 27 */
#define ADC12CSTARTADD_28      (28*0x0001u)   /* ADC12 Conversion Start Address: 28 */
#define ADC12CSTARTADD_29      (29*0x0001u)   /* ADC12 Conversion Start Address: 29 */
#define ADC12CSTARTADD_30      (30*0x0001u)   /* ADC12 Conversion Start Address: 30 */
#define ADC12CSTARTADD_31      (31*0x0001u)   /* ADC12 Conversion Start Address: 31 */

/* ADC12MCTLx Control Bits */
#define ADC12INCH0             (0x0001)       /* ADC12 Input Channel Select Bit 0 */
#define ADC12INCH1             (0x0002)       /* ADC12 Input Channel Select Bit 1 */
#define ADC12INCH2             (0x0004)       /* ADC12 Input Channel Select Bit 2 */
#define ADC12INCH3             (0x0008)       /* ADC12 Input Channel Select Bit 3 */
#define ADC12INCH4             (0x0010)       /* ADC12 Input Channel Select Bit 4 */
#define ADC12EOS               (0x0080)       /* ADC12 End of Sequence */
#define ADC12VRSEL0            (0x0100)       /* ADC12 VR Select Bit 0 */
#define ADC12VRSEL1            (0x0200)       /* ADC12 VR Select Bit 1 */
#define ADC12VRSEL2            (0x0400)       /* ADC12 VR Select Bit 2 */
#define ADC12VRSEL3            (0x0800)       /* ADC12 VR Select Bit 3 */
#define ADC12DIF               (0x2000)       /* ADC12 Differential mode (only for even Registers) */
#define ADC12WINC              (0x4000)       /* ADC12 Comparator window enable */

/* ADC12MCTLx Control Bits */
#define ADC12INCH0_L           (0x0001)       /* ADC12 Input Channel Select Bit 0 */
#define ADC12INCH1_L           (0x0002)       /* ADC12 Input Channel Select Bit 1 */
#define ADC12INCH2_L           (0x0004)       /* ADC12 Input Channel Select Bit 2 */
#define ADC12INCH3_L           (0x0008)       /* ADC12 Input Channel Select Bit 3 */
#define ADC12INCH4_L           (0x0010)       /* ADC12 Input Channel Select Bit 4 */
#define ADC12EOS_L             (0x0080)       /* ADC12 End of Sequence */

/* ADC12MCTLx Control Bits */
#define ADC12VRSEL0_H          (0x0001)       /* ADC12 VR Select Bit 0 */
#define ADC12VRSEL1_H          (0x0002)       /* ADC12 VR Select Bit 1 */
#define ADC12VRSEL2_H          (0x0004)       /* ADC12 VR Select Bit 2 */
#define ADC12VRSEL3_H          (0x0008)       /* ADC12 VR Select Bit 3 */
#define ADC12DIF_H             (0x0020)       /* ADC12 Differential mode (only for even Registers) */
#define ADC12WINC_H            (0x0040)       /* ADC12 Comparator window enable */

#define ADC12INCH_0            (0x0000)       /* ADC12 Input Channel 0 */
#define ADC12INCH_1            (0x0001)       /* ADC12 Input Channel 1 */
#define ADC12INCH_2            (0x0002)       /* ADC12 Input Channel 2 */
#define ADC12INCH_3            (0x0003)       /* ADC12 Input Channel 3 */
#define ADC12INCH_4            (0x0004)       /* ADC12 Input Channel 4 */
#define ADC12INCH_5            (0x0005)       /* ADC12 Input Channel 5 */
#define ADC12INCH_6            (0x0006)       /* ADC12 Input Channel 6 */
#define ADC12INCH_7            (0x0007)       /* ADC12 Input Channel 7 */
#define ADC12INCH_8            (0x0008)       /* ADC12 Input Channel 8 */
#define ADC12INCH_9            (0x0009)       /* ADC12 Input Channel 9 */
#define ADC12INCH_10           (0x000A)       /* ADC12 Input Channel 10 */
#define ADC12INCH_11           (0x000B)       /* ADC12 Input Channel 11 */
#define ADC12INCH_12           (0x000C)       /* ADC12 Input Channel 12 */
#define ADC12INCH_13           (0x000D)       /* ADC12 Input Channel 13 */
#define ADC12INCH_14           (0x000E)       /* ADC12 Input Channel 14 */
#define ADC12INCH_15           (0x000F)       /* ADC12 Input Channel 15 */
#define ADC12INCH_16           (0x0010)       /* ADC12 Input Channel 16 */
#define ADC12INCH_17           (0x0011)       /* ADC12 Input Channel 17 */
#define ADC12INCH_18           (0x0012)       /* ADC12 Input Channel 18 */
#define ADC12INCH_19           (0x0013)       /* ADC12 Input Channel 19 */
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
#define ADC12IE29              (0x2000)       /* ADC12 Memory 29 Interrupt Enable */
#define ADC12IE30              (0x4000)       /* ADC12 Memory 30 Interrupt Enable */
#define ADC12IE31              (0x8000)       /* ADC12 Memory 31 Interrupt Enable */

/* ADC12IER1 Control Bits */
#define ADC12IE16_L            (0x0001)       /* ADC12 Memory 16 Interrupt Enable */
#define ADC12IE17_L            (0x0002)       /* ADC12 Memory 17 Interrupt Enable */
#define ADC12IE18_L            (0x0004)       /* ADC12 Memory 18 Interrupt Enable */
#define ADC12IE19_L            (0x0008)       /* ADC12 Memory 19 Interrupt Enable */
#define ADC12IE20_L            (0x0010)       /* ADC12 Memory 20 Interrupt Enable */
#define ADC12IE21_L            (0x0020)       /* ADC12 Memory 21 Interrupt Enable */
#define ADC12IE22_L            (0x0040)       /* ADC12 Memory 22 Interrupt Enable */
#define ADC12IE23_L            (0x0080)       /* ADC12 Memory 23 Interrupt Enable */

/* ADC12IER1 Control Bits */
#define ADC12IE24_H            (0x0001)       /* ADC12 Memory 24 Interrupt Enable */
#define ADC12IE25_H            (0x0002)       /* ADC12 Memory 25 Interrupt Enable */
#define ADC12IE26_H            (0x0004)       /* ADC12 Memory 26 Interrupt Enable */
#define ADC12IE27_H            (0x0008)       /* ADC12 Memory 27 Interrupt Enable */
#define ADC12IE28_H            (0x0010)       /* ADC12 Memory 28 Interrupt Enable */
#define ADC12IE29_H            (0x0020)       /* ADC12 Memory 29 Interrupt Enable */
#define ADC12IE30_H            (0x0040)       /* ADC12 Memory 30 Interrupt Enable */
#define ADC12IE31_H            (0x0080)       /* ADC12 Memory 31 Interrupt Enable */

/* ADC12IER2 Control Bits */
#define ADC12INIE              (0x0002)       /* ADC12 Interrupt enable for the inside of window of the Window comparator */
#define ADC12LOIE              (0x0004)       /* ADC12 Interrupt enable for lower threshold of the Window comparator */
#define ADC12HIIE              (0x0008)       /* ADC12 Interrupt enable for upper threshold of the Window comparator */
#define ADC12OVIE              (0x0010)       /* ADC12 ADC12MEMx Overflow interrupt enable */
#define ADC12TOVIE             (0x0020)       /* ADC12 Timer Overflow interrupt enable */
#define ADC12RDYIE             (0x0040)       /* ADC12 local buffered reference ready interrupt enable */

/* ADC12IER2 Control Bits */
#define ADC12INIE_L            (0x0002)       /* ADC12 Interrupt enable for the inside of window of the Window comparator */
#define ADC12LOIE_L            (0x0004)       /* ADC12 Interrupt enable for lower threshold of the Window comparator */
#define ADC12HIIE_L            (0x0008)       /* ADC12 Interrupt enable for upper threshold of the Window comparator */
#define ADC12OVIE_L            (0x0010)       /* ADC12 ADC12MEMx Overflow interrupt enable */
#define ADC12TOVIE_L           (0x0020)       /* ADC12 Timer Overflow interrupt enable */
#define ADC12RDYIE_L           (0x0040)       /* ADC12 local buffered reference ready interrupt enable */

/* ADC12IFGR0 Control Bits */
#define ADC12IFG0              (0x0001)       /* ADC12 Memory 0 Interrupt Flag */
#define ADC12IFG1              (0x0002)       /* ADC12 Memory 1 Interrupt Flag */
#define ADC12IFG2              (0x0004)       /* ADC12 Memory 2 Interrupt Flag */
#define ADC12IFG3              (0x0008)       /* ADC12 Memory 3 Interrupt Flag */
#define ADC12IFG4              (0x0010)       /* ADC12 Memory 4 Interrupt Flag */
#define ADC12IFG5              (0x0020)       /* ADC12 Memory 5 Interrupt Flag */
#define ADC12IFG6              (0x0040)       /* ADC12 Memory 6 Interrupt Flag */
#define ADC12IFG7              (0x0080)       /* ADC12 Memory 7 Interrupt Flag */
#define ADC12IFG8              (0x0100)       /* ADC12 Memory 8 Interrupt Flag */
#define ADC12IFG9              (0x0200)       /* ADC12 Memory 9 Interrupt Flag */
#define ADC12IFG10             (0x0400)       /* ADC12 Memory 10 Interrupt Flag */
#define ADC12IFG11             (0x0800)       /* ADC12 Memory 11 Interrupt Flag */
#define ADC12IFG12             (0x1000)       /* ADC12 Memory 12 Interrupt Flag */
#define ADC12IFG13             (0x2000)       /* ADC12 Memory 13 Interrupt Flag */
#define ADC12IFG14             (0x4000)       /* ADC12 Memory 14 Interrupt Flag */
#define ADC12IFG15             (0x8000)       /* ADC12 Memory 15 Interrupt Flag */

/* ADC12IFGR0 Control Bits */
#define ADC12IFG0_L            (0x0001)       /* ADC12 Memory 0 Interrupt Flag */
#define ADC12IFG1_L            (0x0002)       /* ADC12 Memory 1 Interrupt Flag */
#define ADC12IFG2_L            (0x0004)       /* ADC12 Memory 2 Interrupt Flag */
#define ADC12IFG3_L            (0x0008)       /* ADC12 Memory 3 Interrupt Flag */
#define ADC12IFG4_L            (0x0010)       /* ADC12 Memory 4 Interrupt Flag */
#define ADC12IFG5_L            (0x0020)       /* ADC12 Memory 5 Interrupt Flag */
#define ADC12IFG6_L            (0x0040)       /* ADC12 Memory 6 Interrupt Flag */
#define ADC12IFG7_L            (0x0080)       /* ADC12 Memory 7 Interrupt Flag */

/* ADC12IFGR0 Control Bits */
#define ADC12IFG8_H            (0x0001)       /* ADC12 Memory 8 Interrupt Flag */
#define ADC12IFG9_H            (0x0002)       /* ADC12 Memory 9 Interrupt Flag */
#define ADC12IFG10_H           (0x0004)       /* ADC12 Memory 10 Interrupt Flag */
#define ADC12IFG11_H           (0x0008)       /* ADC12 Memory 11 Interrupt Flag */
#define ADC12IFG12_H           (0x0010)       /* ADC12 Memory 12 Interrupt Flag */
#define ADC12IFG13_H           (0x0020)       /* ADC12 Memory 13 Interrupt Flag */
#define ADC12IFG14_H           (0x0040)       /* ADC12 Memory 14 Interrupt Flag */
#define ADC12IFG15_H           (0x0080)       /* ADC12 Memory 15 Interrupt Flag */

/* ADC12IFGR1 Control Bits */
#define ADC12IFG16             (0x0001)       /* ADC12 Memory 16 Interrupt Flag */
#define ADC12IFG17             (0x0002)       /* ADC12 Memory 17 Interrupt Flag */
#define ADC12IFG18             (0x0004)       /* ADC12 Memory 18 Interrupt Flag */
#define ADC12IFG19             (0x0008)       /* ADC12 Memory 19 Interrupt Flag */
#define ADC12IFG20             (0x0010)       /* ADC12 Memory 20 Interrupt Flag */
#define ADC12IFG21             (0x0020)       /* ADC12 Memory 21 Interrupt Flag */
#define ADC12IFG22             (0x0040)       /* ADC12 Memory 22 Interrupt Flag */
#define ADC12IFG23             (0x0080)       /* ADC12 Memory 23 Interrupt Flag */
#define ADC12IFG24             (0x0100)       /* ADC12 Memory 24 Interrupt Flag */
#define ADC12IFG25             (0x0200)       /* ADC12 Memory 25 Interrupt Flag */
#define ADC12IFG26             (0x0400)       /* ADC12 Memory 26 Interrupt Flag */
#define ADC12IFG27             (0x0800)       /* ADC12 Memory 27 Interrupt Flag */
#define ADC12IFG28             (0x1000)       /* ADC12 Memory 28 Interrupt Flag */
#define ADC12IFG29             (0x2000)       /* ADC12 Memory 29 Interrupt Flag */
#define ADC12IFG30             (0x4000)       /* ADC12 Memory 30 Interrupt Flag */
#define ADC12IFG31             (0x8000)       /* ADC12 Memory 31 Interrupt Flag */

/* ADC12IFGR1 Control Bits */
#define ADC12IFG16_L           (0x0001)       /* ADC12 Memory 16 Interrupt Flag */
#define ADC12IFG17_L           (0x0002)       /* ADC12 Memory 17 Interrupt Flag */
#define ADC12IFG18_L           (0x0004)       /* ADC12 Memory 18 Interrupt Flag */
#define ADC12IFG19_L           (0x0008)       /* ADC12 Memory 19 Interrupt Flag */
#define ADC12IFG20_L           (0x0010)       /* ADC12 Memory 20 Interrupt Flag */
#define ADC12IFG21_L           (0x0020)       /* ADC12 Memory 21 Interrupt Flag */
#define ADC12IFG22_L           (0x0040)       /* ADC12 Memory 22 Interrupt Flag */
#define ADC12IFG23_L           (0x0080)       /* ADC12 Memory 23 Interrupt Flag */

/* ADC12IFGR1 Control Bits */
#define ADC12IFG24_H           (0x0001)       /* ADC12 Memory 24 Interrupt Flag */
#define ADC12IFG25_H           (0x0002)       /* ADC12 Memory 25 Interrupt Flag */
#define ADC12IFG26_H           (0x0004)       /* ADC12 Memory 26 Interrupt Flag */
#define ADC12IFG27_H           (0x0008)       /* ADC12 Memory 27 Interrupt Flag */
#define ADC12IFG28_H           (0x0010)       /* ADC12 Memory 28 Interrupt Flag */
#define ADC12IFG29_H           (0x0020)       /* ADC12 Memory 29 Interrupt Flag */
#define ADC12IFG30_H           (0x0040)       /* ADC12 Memory 30 Interrupt Flag */
#define ADC12IFG31_H           (0x0080)       /* ADC12 Memory 31 Interrupt Flag */

/* ADC12IFGR2 Control Bits */
#define ADC12INIFG             (0x0002)       /* ADC12 Interrupt Flag for the inside of window of the Window comparator */
#define ADC12LOIFG             (0x0004)       /* ADC12 Interrupt Flag for lower threshold of the Window comparator */
#define ADC12HIIFG             (0x0008)       /* ADC12 Interrupt Flag for upper threshold of the Window comparator */
#define ADC12OVIFG             (0x0010)       /* ADC12 ADC12MEMx Overflow interrupt Flag */
#define ADC12TOVIFG            (0x0020)       /* ADC12 Timer Overflow interrupt Flag */
#define ADC12RDYIFG            (0x0040)       /* ADC12 local buffered reference ready interrupt Flag */

/* ADC12IFGR2 Control Bits */
#define ADC12INIFG_L           (0x0002)       /* ADC12 Interrupt Flag for the inside of window of the Window comparator */
#define ADC12LOIFG_L           (0x0004)       /* ADC12 Interrupt Flag for lower threshold of the Window comparator */
#define ADC12HIIFG_L           (0x0008)       /* ADC12 Interrupt Flag for upper threshold of the Window comparator */
#define ADC12OVIFG_L           (0x0010)       /* ADC12 ADC12MEMx Overflow interrupt Flag */
#define ADC12TOVIFG_L          (0x0020)       /* ADC12 Timer Overflow interrupt Flag */
#define ADC12RDYIFG_L          (0x0040)       /* ADC12 local buffered reference ready interrupt Flag */

/* ADC12IV Definitions */
#define ADC12IV_NONE           (0x0000)       /* No Interrupt pending */
#define ADC12IV_ADC12OVIFG     (0x0002)       /* ADC12OVIFG */
#define ADC12IV_ADC12TOVIFG    (0x0004)       /* ADC12TOVIFG */
#define ADC12IV_ADC12HIIFG     (0x0006)       /* ADC12HIIFG */
#define ADC12IV_ADC12LOIFG     (0x0008)       /* ADC12LOIFG */
#define ADC12IV_ADC12INIFG     (0x000A)       /* ADC12INIFG */
#define ADC12IV_ADC12IFG0      (0x000C)       /* ADC12IFG0 */
#define ADC12IV_ADC12IFG1      (0x000E)       /* ADC12IFG1 */
#define ADC12IV_ADC12IFG2      (0x0010)       /* ADC12IFG2 */
#define ADC12IV_ADC12IFG3      (0x0012)       /* ADC12IFG3 */
#define ADC12IV_ADC12IFG4      (0x0014)       /* ADC12IFG4 */
#define ADC12IV_ADC12IFG5      (0x0016)       /* ADC12IFG5 */
#define ADC12IV_ADC12IFG6      (0x0018)       /* ADC12IFG6 */
#define ADC12IV_ADC12IFG7      (0x001A)       /* ADC12IFG7 */
#define ADC12IV_ADC12IFG8      (0x001C)       /* ADC12IFG8 */
#define ADC12IV_ADC12IFG9      (0x001E)       /* ADC12IFG9 */
#define ADC12IV_ADC12IFG10     (0x0020)       /* ADC12IFG10 */
#define ADC12IV_ADC12IFG11     (0x0022)       /* ADC12IFG11 */
#define ADC12IV_ADC12IFG12     (0x0024)       /* ADC12IFG12 */
#define ADC12IV_ADC12IFG13     (0x0026)       /* ADC12IFG13 */
#define ADC12IV_ADC12IFG14     (0x0028)       /* ADC12IFG14 */
#define ADC12IV_ADC12IFG15     (0x002A)       /* ADC12IFG15 */
#define ADC12IV_ADC12IFG16     (0x002C)       /* ADC12IFG16 */
#define ADC12IV_ADC12IFG17     (0x002E)       /* ADC12IFG17 */
#define ADC12IV_ADC12IFG18     (0x0030)       /* ADC12IFG18 */
#define ADC12IV_ADC12IFG19     (0x0032)       /* ADC12IFG19 */
#define ADC12IV_ADC12IFG20     (0x0034)       /* ADC12IFG20 */
#define ADC12IV_ADC12IFG21     (0x0036)       /* ADC12IFG21 */
#define ADC12IV_ADC12IFG22     (0x0038)       /* ADC12IFG22 */
#define ADC12IV_ADC12IFG23     (0x003A)       /* ADC12IFG23 */
#define ADC12IV_ADC12IFG24     (0x003C)       /* ADC12IFG24 */
#define ADC12IV_ADC12IFG25     (0x003E)       /* ADC12IFG25 */
#define ADC12IV_ADC12IFG26     (0x0040)       /* ADC12IFG26 */
#define ADC12IV_ADC12IFG27     (0x0042)       /* ADC12IFG27 */
#define ADC12IV_ADC12IFG28     (0x0044)       /* ADC12IFG28 */
#define ADC12IV_ADC12IFG29     (0x0046)       /* ADC12IFG29 */
#define ADC12IV_ADC12IFG30     (0x0048)       /* ADC12IFG30 */
#define ADC12IV_ADC12IFG31     (0x004A)       /* ADC12IFG31 */
#define ADC12IV_ADC12RDYIFG    (0x004C)       /* ADC12RDYIFG */


/************************************************************
* AES256 Accelerator
************************************************************/
#define __MSP430_HAS_AES256__                 /* Definition to show that Module is available */
#define __MSP430_BASEADDRESS_AES256__ 0x09C0
#define AES256_BASE            __MSP430_BASEADDRESS_AES256__

SFR_16BIT(AESACTL0);                          /* AES accelerator control register 0 */
SFR_8BIT(AESACTL0_L);                         /* AES accelerator control register 0 */
SFR_8BIT(AESACTL0_H);                         /* AES accelerator control register 0 */
SFR_16BIT(AESACTL1);                          /* AES accelerator control register 1 */
SFR_8BIT(AESACTL1_L);                         /* AES accelerator control register 1 */
SFR_8BIT(AESACTL1_H);                         /* AES accelerator control register 1 */
SFR_16BIT(AESASTAT);                          /* AES accelerator status register */
SFR_8BIT(AESASTAT_L);                         /* AES accelerator status register */
SFR_8BIT(AESASTAT_H);                         /* AES accelerator status register */
SFR_16BIT(AESAKEY);                           /* AES accelerator key register */
SFR_8BIT(AESAKEY_L);                          /* AES accelerator key register */
SFR_8BIT(AESAKEY_H);                          /* AES accelerator key register */
SFR_16BIT(AESADIN);                           /* AES accelerator data in register */
SFR_8BIT(AESADIN_L);                          /* AES accelerator data in register */
SFR_8BIT(AESADIN_H);                          /* AES accelerator data in register */
SFR_16BIT(AESADOUT);                          /* AES accelerator data out register  */
SFR_8BIT(AESADOUT_L);                         /* AES accelerator data out register  */
SFR_8BIT(AESADOUT_H);                         /* AES accelerator data out register  */
SFR_16BIT(AESAXDIN);                          /* AES accelerator XORed data in register */
SFR_8BIT(AESAXDIN_L);                         /* AES accelerator XORed data in register */
SFR_8BIT(AESAXDIN_H);                         /* AES accelerator XORed data in register */
SFR_16BIT(AESAXIN);                           /* AES accelerator XORed data in register (no trigger)  */
SFR_8BIT(AESAXIN_L);                          /* AES accelerator XORed data in register (no trigger)  */
SFR_8BIT(AESAXIN_H);                          /* AES accelerator XORed data in register (no trigger)  */

/* AESACTL0 Control Bits */
#define AESOP0                 (0x0001)       /* AES Operation Bit: 0 */
#define AESOP1                 (0x0002)       /* AES Operation Bit: 1 */
#define AESKL0                 (0x0004)       /* AES Key length Bit: 0 */
#define AESKL1                 (0x0008)       /* AES Key length Bit: 1 */
#define AESTRIG                (0x0010)       /* AES Trigger Select */
#define AESCM0                 (0x0020)       /* AES Cipher mode select Bit: 0 */
#define AESCM1                 (0x0040)       /* AES Cipher mode select Bit: 1 */
#define AESSWRST               (0x0080)       /* AES Software Reset */
#define AESRDYIFG              (0x0100)       /* AES ready interrupt flag */
#define AESERRFG               (0x0800)       /* AES Error Flag */
#define AESRDYIE               (0x1000)       /* AES ready interrupt enable*/
#define AESCMEN                (0x8000)       /* AES DMA cipher mode enable*/

/* AESACTL0 Control Bits */
#define AESOP0_L               (0x0001)       /* AES Operation Bit: 0 */
#define AESOP1_L               (0x0002)       /* AES Operation Bit: 1 */
#define AESKL0_L               (0x0004)       /* AES Key length Bit: 0 */
#define AESKL1_L               (0x0008)       /* AES Key length Bit: 1 */
#define AESTRIG_L              (0x0010)       /* AES Trigger Select */
#define AESCM0_L               (0x0020)       /* AES Cipher mode select Bit: 0 */
#define AESCM1_L               (0x0040)       /* AES Cipher mode select Bit: 1 */
#define AESSWRST_L             (0x0080)       /* AES Software Reset */

/* AESACTL0 Control Bits */
#define AESRDYIFG_H            (0x0001)       /* AES ready interrupt flag */
#define AESERRFG_H             (0x0008)       /* AES Error Flag */
#define AESRDYIE_H             (0x0010)       /* AES ready interrupt enable*/
#define AESCMEN_H              (0x0080)       /* AES DMA cipher mode enable*/

#define AESOP_0                (0x0000)       /* AES Operation: Encrypt */
#define AESOP_1                (0x0001)       /* AES Operation: Decrypt (same Key) */
#define AESOP_2                (0x0002)       /* AES Operation: Generate first round Key */
#define AESOP_3                (0x0003)       /* AES Operation: Decrypt (first round Key) */

#define AESKL_0                (0x0000)       /* AES Key length: AES128 */
#define AESKL_1                (0x0004)       /* AES Key length: AES192 */
#define AESKL_2                (0x0008)       /* AES Key length: AES256 */
#define AESKL__128             (0x0000)       /* AES Key length: AES128 */
#define AESKL__192             (0x0004)       /* AES Key length: AES192 */
#define AESKL__256             (0x0008)       /* AES Key length: AES256 */

#define AESCM_0                (0x0000)       /* AES Cipher mode select: ECB */
#define AESCM_1                (0x0020)       /* AES Cipher mode select: CBC */
#define AESCM_2                (0x0040)       /* AES Cipher mode select: OFB */
#define AESCM_3                (0x0060)       /* AES Cipher mode select: CFB */
#define AESCM__ECB             (0x0000)       /* AES Cipher mode select: ECB */
#define AESCM__CBC             (0x0020)       /* AES Cipher mode select: CBC */
#define AESCM__OFB             (0x0040)       /* AES Cipher mode select: OFB */
#define AESCM__CFB             (0x0060)       /* AES Cipher mode select: CFB */

/* AESACTL1 Control Bits */
#define AESBLKCNT0             (0x0001)       /* AES Cipher Block Counter Bit: 0 */
#define AESBLKCNT1             (0x0002)       /* AES Cipher Block Counter Bit: 1 */
#define AESBLKCNT2             (0x0004)       /* AES Cipher Block Counter Bit: 2 */
#define AESBLKCNT3             (0x0008)       /* AES Cipher Block Counter Bit: 3 */
#define AESBLKCNT4             (0x0010)       /* AES Cipher Block Counter Bit: 4 */
#define AESBLKCNT5             (0x0020)       /* AES Cipher Block Counter Bit: 5 */
#define AESBLKCNT6             (0x0040)       /* AES Cipher Block Counter Bit: 6 */
#define AESBLKCNT7             (0x0080)       /* AES Cipher Block Counter Bit: 7 */

/* AESACTL1 Control Bits */
#define AESBLKCNT0_L           (0x0001)       /* AES Cipher Block Counter Bit: 0 */
#define AESBLKCNT1_L           (0x0002)       /* AES Cipher Block Counter Bit: 1 */
#define AESBLKCNT2_L           (0x0004)       /* AES Cipher Block Counter Bit: 2 */
#define AESBLKCNT3_L           (0x0008)       /* AES Cipher Block Counter Bit: 3 */
#define AESBLKCNT4_L           (0x0010)       /* AES Cipher Block Counter Bit: 4 */
#define AESBLKCNT5_L           (0x0020)       /* AES Cipher Block Counter Bit: 5 */
#define AESBLKCNT6_L           (0x0040)       /* AES Cipher Block Counter Bit: 6 */
#define AESBLKCNT7_L           (0x0080)       /* AES Cipher Block Counter Bit: 7 */

/* AESASTAT Control Bits */
#define AESBUSY                (0x0001)       /* AES Busy */
#define AESKEYWR               (0x0002)       /* AES All 16 bytes written to AESAKEY */
#define AESDINWR               (0x0004)       /* AES All 16 bytes written to AESADIN */
#define AESDOUTRD              (0x0008)       /* AES All 16 bytes read from AESADOUT */
#define AESKEYCNT0             (0x0010)       /* AES Bytes written via AESAKEY Bit: 0 */
#define AESKEYCNT1             (0x0020)       /* AES Bytes written via AESAKEY Bit: 1 */
#define AESKEYCNT2             (0x0040)       /* AES Bytes written via AESAKEY Bit: 2 */
#define AESKEYCNT3             (0x0080)       /* AES Bytes written via AESAKEY Bit: 3 */
#define AESDINCNT0             (0x0100)       /* AES Bytes written via AESADIN Bit: 0 */
#define AESDINCNT1             (0x0200)       /* AES Bytes written via AESADIN Bit: 1 */
#define AESDINCNT2             (0x0400)       /* AES Bytes written via AESADIN Bit: 2 */
#define AESDINCNT3             (0x0800)       /* AES Bytes written via AESADIN Bit: 3 */
#define AESDOUTCNT0            (0x1000)       /* AES Bytes read via AESADOUT Bit: 0 */
#define AESDOUTCNT1            (0x2000)       /* AES Bytes read via AESADOUT Bit: 1 */
#define AESDOUTCNT2            (0x4000)       /* AES Bytes read via AESADOUT Bit: 2 */
#define AESDOUTCNT3            (0x8000)       /* AES Bytes read via AESADOUT Bit: 3 */

/* AESASTAT Control Bits */
#define AESBUSY_L              (0x0001)       /* AES Busy */
#define AESKEYWR_L             (0x0002)       /* AES All 16 bytes written to AESAKEY */
#define AESDINWR_L             (0x0004)       /* AES All 16 bytes written to AESADIN */
#define AESDOUTRD_L            (0x0008)       /* AES All 16 bytes read from AESADOUT */
#define AESKEYCNT0_L           (0x0010)       /* AES Bytes written via AESAKEY Bit: 0 */
#define AESKEYCNT1_L           (0x0020)       /* AES Bytes written via AESAKEY Bit: 1 */
#define AESKEYCNT2_L           (0x0040)       /* AES Bytes written via AESAKEY Bit: 2 */
#define AESKEYCNT3_L           (0x0080)       /* AES Bytes written via AESAKEY Bit: 3 */

/* AESASTAT Control Bits */
#define AESDINCNT0_H           (0x0001)       /* AES Bytes written via AESADIN Bit: 0 */
#define AESDINCNT1_H           (0x0002)       /* AES Bytes written via AESADIN Bit: 1 */
#define AESDINCNT2_H           (0x0004)       /* AES Bytes written via AESADIN Bit: 2 */
#define AESDINCNT3_H           (0x0008)       /* AES Bytes written via AESADIN Bit: 3 */
#define AESDOUTCNT0_H          (0x0010)       /* AES Bytes read via AESADOUT Bit: 0 */
#define AESDOUTCNT1_H          (0x0020)       /* AES Bytes read via AESADOUT Bit: 1 */
#define AESDOUTCNT2_H          (0x0040)       /* AES Bytes read via AESADOUT Bit: 2 */
#define AESDOUTCNT3_H          (0x0080)       /* AES Bytes read via AESADOUT Bit: 3 */

/************************************************************
* Capacitive_Touch_IO 0
************************************************************/
#define __MSP430_HAS_CAP_TOUCH_IO_0__                /* Definition to show that Module is available */
#define __MSP430_BASEADDRESS_CAP_TOUCH_IO_0__ 0x0430
#define CAP_TOUCH_0_BASE       __MSP430_BASEADDRESS_CAP_TOUCH_IO_0__

SFR_16BIT(CAPTIO0CTL);                        /* Capacitive_Touch_IO 0 control register */
SFR_8BIT(CAPTIO0CTL_L);                       /* Capacitive_Touch_IO 0 control register */
SFR_8BIT(CAPTIO0CTL_H);                       /* Capacitive_Touch_IO 0 control register */

#define  CAPSIO0CTL            CAPTIO0CTL     /* legacy define */

/************************************************************
* Capacitive_Touch_IO 1
************************************************************/
#define __MSP430_HAS_CAP_TOUCH_IO_1__                /* Definition to show that Module is available */
#define __MSP430_BASEADDRESS_CAP_TOUCH_IO_1__ 0x0470
#define CAP_TOUCH_1_BASE       __MSP430_BASEADDRESS_CAP_TOUCH_IO_1__

SFR_16BIT(CAPTIO1CTL);                        /* Capacitive_Touch_IO 1 control register */
SFR_8BIT(CAPTIO1CTL_L);                       /* Capacitive_Touch_IO 1 control register */
SFR_8BIT(CAPTIO1CTL_H);                       /* Capacitive_Touch_IO 1 control register */

#define  CAPSIO1CTL            CAPTIO1CTL     /* legacy define */

/* CAPTIOxCTL Control Bits */
#define CAPTIOPISEL0           (0x0002)       /* CapTouchIO Pin Select Bit: 0 */
#define CAPTIOPISEL1           (0x0004)       /* CapTouchIO Pin Select Bit: 1 */
#define CAPTIOPISEL2           (0x0008)       /* CapTouchIO Pin Select Bit: 2 */
#define CAPTIOPOSEL0           (0x0010)       /* CapTouchIO Port Select Bit: 0 */
#define CAPTIOPOSEL1           (0x0020)       /* CapTouchIO Port Select Bit: 1 */
#define CAPTIOPOSEL2           (0x0040)       /* CapTouchIO Port Select Bit: 2 */
#define CAPTIOPOSEL3           (0x0080)       /* CapTouchIO Port Select Bit: 3 */
#define CAPTIOEN               (0x0100)       /* CapTouchIO Enable */
#define CAPTIO                 (0x0200)       /* CapTouchIO state */

/* CAPTIOxCTL Control Bits */
#define CAPTIOPISEL0_L         (0x0002)       /* CapTouchIO Pin Select Bit: 0 */
#define CAPTIOPISEL1_L         (0x0004)       /* CapTouchIO Pin Select Bit: 1 */
#define CAPTIOPISEL2_L         (0x0008)       /* CapTouchIO Pin Select Bit: 2 */
#define CAPTIOPOSEL0_L         (0x0010)       /* CapTouchIO Port Select Bit: 0 */
#define CAPTIOPOSEL1_L         (0x0020)       /* CapTouchIO Port Select Bit: 1 */
#define CAPTIOPOSEL2_L         (0x0040)       /* CapTouchIO Port Select Bit: 2 */
#define CAPTIOPOSEL3_L         (0x0080)       /* CapTouchIO Port Select Bit: 3 */

/* CAPTIOxCTL Control Bits */
#define CAPTIOEN_H             (0x0001)       /* CapTouchIO Enable */
#define CAPTIO_H               (0x0002)       /* CapTouchIO state */

/* Legacy defines */
#define CAPSIOPISEL0           (0x0002)       /* CapTouchIO Pin Select Bit: 0 */
#define CAPSIOPISEL1           (0x0004)       /* CapTouchIO Pin Select Bit: 1 */
#define CAPSIOPISEL2           (0x0008)       /* CapTouchIO Pin Select Bit: 2 */
#define CAPSIOPOSEL0           (0x0010)       /* CapTouchIO Port Select Bit: 0 */
#define CAPSIOPOSEL1           (0x0020)       /* CapTouchIO Port Select Bit: 1 */
#define CAPSIOPOSEL2           (0x0040)       /* CapTouchIO Port Select Bit: 2 */
#define CAPSIOPOSEL3           (0x0080)       /* CapTouchIO Port Select Bit: 3 */
#define CAPSIOEN               (0x0100)       /* CapTouchIO Enable */
#define CAPSIO                 (0x0200)       /* CapTouchIO state */

/************************************************************
* Comparator E
************************************************************/
#define __MSP430_HAS_COMP_E__                 /* Definition to show that Module is available */
#define __MSP430_BASEADDRESS_COMP_E__ 0x08C0
#define COMP_E_BASE            __MSP430_BASEADDRESS_COMP_E__

SFR_16BIT(CECTL0);                            /* Comparator E Control Register 0 */
SFR_8BIT(CECTL0_L);                           /* Comparator E Control Register 0 */
SFR_8BIT(CECTL0_H);                           /* Comparator E Control Register 0 */
SFR_16BIT(CECTL1);                            /* Comparator E Control Register 1 */
SFR_8BIT(CECTL1_L);                           /* Comparator E Control Register 1 */
SFR_8BIT(CECTL1_H);                           /* Comparator E Control Register 1 */
SFR_16BIT(CECTL2);                            /* Comparator E Control Register 2 */
SFR_8BIT(CECTL2_L);                           /* Comparator E Control Register 2 */
SFR_8BIT(CECTL2_H);                           /* Comparator E Control Register 2 */
SFR_16BIT(CECTL3);                            /* Comparator E Control Register 3 */
SFR_8BIT(CECTL3_L);                           /* Comparator E Control Register 3 */
SFR_8BIT(CECTL3_H);                           /* Comparator E Control Register 3 */
SFR_16BIT(CEINT);                             /* Comparator E Interrupt Register */
SFR_8BIT(CEINT_L);                            /* Comparator E Interrupt Register */
SFR_8BIT(CEINT_H);                            /* Comparator E Interrupt Register */
SFR_16BIT(CEIV);                              /* Comparator E Interrupt Vector Word */
SFR_8BIT(CEIV_L);                             /* Comparator E Interrupt Vector Word */
SFR_8BIT(CEIV_H);                             /* Comparator E Interrupt Vector Word */

/* CECTL0 Control Bits */
#define CEIPSEL0               (0x0001)       /* Comp. E Pos. Channel Input Select 0 */
#define CEIPSEL1               (0x0002)       /* Comp. E Pos. Channel Input Select 1 */
#define CEIPSEL2               (0x0004)       /* Comp. E Pos. Channel Input Select 2 */
#define CEIPSEL3               (0x0008)       /* Comp. E Pos. Channel Input Select 3 */
//#define RESERVED            (0x0010)  /* Comp. E */
//#define RESERVED            (0x0020)  /* Comp. E */
//#define RESERVED            (0x0040)  /* Comp. E */
#define CEIPEN                 (0x0080)       /* Comp. E Pos. Channel Input Enable */
#define CEIMSEL0               (0x0100)       /* Comp. E Neg. Channel Input Select 0 */
#define CEIMSEL1               (0x0200)       /* Comp. E Neg. Channel Input Select 1 */
#define CEIMSEL2               (0x0400)       /* Comp. E Neg. Channel Input Select 2 */
#define CEIMSEL3               (0x0800)       /* Comp. E Neg. Channel Input Select 3 */
//#define RESERVED            (0x1000)  /* Comp. E */
//#define RESERVED            (0x2000)  /* Comp. E */
//#define RESERVED            (0x4000)  /* Comp. E */
#define CEIMEN                 (0x8000)       /* Comp. E Neg. Channel Input Enable */

/* CECTL0 Control Bits */
#define CEIPSEL0_L             (0x0001)       /* Comp. E Pos. Channel Input Select 0 */
#define CEIPSEL1_L             (0x0002)       /* Comp. E Pos. Channel Input Select 1 */
#define CEIPSEL2_L             (0x0004)       /* Comp. E Pos. Channel Input Select 2 */
#define CEIPSEL3_L             (0x0008)       /* Comp. E Pos. Channel Input Select 3 */
//#define RESERVED            (0x0010)  /* Comp. E */
//#define RESERVED            (0x0020)  /* Comp. E */
//#define RESERVED            (0x0040)  /* Comp. E */
#define CEIPEN_L               (0x0080)       /* Comp. E Pos. Channel Input Enable */
//#define RESERVED            (0x1000)  /* Comp. E */
//#define RESERVED            (0x2000)  /* Comp. E */
//#define RESERVED            (0x4000)  /* Comp. E */

/* CECTL0 Control Bits */
//#define RESERVED            (0x0010)  /* Comp. E */
//#define RESERVED            (0x0020)  /* Comp. E */
//#define RESERVED            (0x0040)  /* Comp. E */
#define CEIMSEL0_H             (0x0001)       /* Comp. E Neg. Channel Input Select 0 */
#define CEIMSEL1_H             (0x0002)       /* Comp. E Neg. Channel Input Select 1 */
#define CEIMSEL2_H             (0x0004)       /* Comp. E Neg. Channel Input Select 2 */
#define CEIMSEL3_H             (0x0008)       /* Comp. E Neg. Channel Input Select 3 */
//#define RESERVED            (0x1000)  /* Comp. E */
//#define RESERVED            (0x2000)  /* Comp. E */
//#define RESERVED            (0x4000)  /* Comp. E */
#define CEIMEN_H               (0x0080)       /* Comp. E Neg. Channel Input Enable */

#define CEIPSEL_0              (0x0000)       /* Comp. E V+ terminal Input Select: Channel 0 */
#define CEIPSEL_1              (0x0001)       /* Comp. E V+ terminal Input Select: Channel 1 */
#define CEIPSEL_2              (0x0002)       /* Comp. E V+ terminal Input Select: Channel 2 */
#define CEIPSEL_3              (0x0003)       /* Comp. E V+ terminal Input Select: Channel 3 */
#define CEIPSEL_4              (0x0004)       /* Comp. E V+ terminal Input Select: Channel 4 */
#define CEIPSEL_5              (0x0005)       /* Comp. E V+ terminal Input Select: Channel 5 */
#define CEIPSEL_6              (0x0006)       /* Comp. E V+ terminal Input Select: Channel 6 */
#define CEIPSEL_7              (0x0007)       /* Comp. E V+ terminal Input Select: Channel 7 */
#define CEIPSEL_8              (0x0008)       /* Comp. E V+ terminal Input Select: Channel 8 */
#define CEIPSEL_9              (0x0009)       /* Comp. E V+ terminal Input Select: Channel 9 */
#define CEIPSEL_10             (0x000A)       /* Comp. E V+ terminal Input Select: Channel 10 */
#define CEIPSEL_11             (0x000B)       /* Comp. E V+ terminal Input Select: Channel 11 */
#define CEIPSEL_12             (0x000C)       /* Comp. E V+ terminal Input Select: Channel 12 */
#define CEIPSEL_13             (0x000D)       /* Comp. E V+ terminal Input Select: Channel 13 */
#define CEIPSEL_14             (0x000E)       /* Comp. E V+ terminal Input Select: Channel 14 */
#define CEIPSEL_15             (0x000F)       /* Comp. E V+ terminal Input Select: Channel 15 */

#define CEIMSEL_0              (0x0000)       /* Comp. E V- Terminal Input Select: Channel 0 */
#define CEIMSEL_1              (0x0100)       /* Comp. E V- Terminal Input Select: Channel 1 */
#define CEIMSEL_2              (0x0200)       /* Comp. E V- Terminal Input Select: Channel 2 */
#define CEIMSEL_3              (0x0300)       /* Comp. E V- Terminal Input Select: Channel 3 */
#define CEIMSEL_4              (0x0400)       /* Comp. E V- Terminal Input Select: Channel 4 */
#define CEIMSEL_5              (0x0500)       /* Comp. E V- Terminal Input Select: Channel 5 */
#define CEIMSEL_6              (0x0600)       /* Comp. E V- Terminal Input Select: Channel 6 */
#define CEIMSEL_7              (0x0700)       /* Comp. E V- Terminal Input Select: Channel 7 */
#define CEIMSEL_8              (0x0800)       /* Comp. E V- terminal Input Select: Channel 8 */
#define CEIMSEL_9              (0x0900)       /* Comp. E V- terminal Input Select: Channel 9 */
#define CEIMSEL_10             (0x0A00)       /* Comp. E V- terminal Input Select: Channel 10 */
#define CEIMSEL_11             (0x0B00)       /* Comp. E V- terminal Input Select: Channel 11 */
#define CEIMSEL_12             (0x0C00)       /* Comp. E V- terminal Input Select: Channel 12 */
#define CEIMSEL_13             (0x0D00)       /* Comp. E V- terminal Input Select: Channel 13 */
#define CEIMSEL_14             (0x0E00)       /* Comp. E V- terminal Input Select: Channel 14 */
#define CEIMSEL_15             (0x0F00)       /* Comp. E V- terminal Input Select: Channel 15 */

/* CECTL1 Control Bits */
#define CEOUT                  (0x0001)       /* Comp. E Output */
#define CEOUTPOL               (0x0002)       /* Comp. E Output Polarity */
#define CEF                    (0x0004)       /* Comp. E Enable Output Filter */
#define CEIES                  (0x0008)       /* Comp. E Interrupt Edge Select */
#define CESHORT                (0x0010)       /* Comp. E Input Short */
#define CEEX                   (0x0020)       /* Comp. E Exchange Inputs */
#define CEFDLY0                (0x0040)       /* Comp. E Filter delay Bit 0 */
#define CEFDLY1                (0x0080)       /* Comp. E Filter delay Bit 1 */
#define CEPWRMD0               (0x0100)       /* Comp. E Power mode Bit 0 */
#define CEPWRMD1               (0x0200)       /* Comp. E Power mode Bit 1 */
#define CEON                   (0x0400)       /* Comp. E enable */
#define CEMRVL                 (0x0800)       /* Comp. E CEMRV Level */
#define CEMRVS                 (0x1000)       /* Comp. E Output selects between VREF0 or VREF1*/
//#define RESERVED            (0x2000)  /* Comp. E */
//#define RESERVED            (0x4000)  /* Comp. E */
//#define RESERVED            (0x8000)  /* Comp. E */

/* CECTL1 Control Bits */
#define CEOUT_L                (0x0001)       /* Comp. E Output */
#define CEOUTPOL_L             (0x0002)       /* Comp. E Output Polarity */
#define CEF_L                  (0x0004)       /* Comp. E Enable Output Filter */
#define CEIES_L                (0x0008)       /* Comp. E Interrupt Edge Select */
#define CESHORT_L              (0x0010)       /* Comp. E Input Short */
#define CEEX_L                 (0x0020)       /* Comp. E Exchange Inputs */
#define CEFDLY0_L              (0x0040)       /* Comp. E Filter delay Bit 0 */
#define CEFDLY1_L              (0x0080)       /* Comp. E Filter delay Bit 1 */
//#define RESERVED            (0x2000)  /* Comp. E */
//#define RESERVED            (0x4000)  /* Comp. E */
//#define RESERVED            (0x8000)  /* Comp. E */

/* CECTL1 Control Bits */
#define CEPWRMD0_H             (0x0001)       /* Comp. E Power mode Bit 0 */
#define CEPWRMD1_H             (0x0002)       /* Comp. E Power mode Bit 1 */
#define CEON_H                 (0x0004)       /* Comp. E enable */
#define CEMRVL_H               (0x0008)       /* Comp. E CEMRV Level */
#define CEMRVS_H               (0x0010)       /* Comp. E Output selects between VREF0 or VREF1*/
//#define RESERVED            (0x2000)  /* Comp. E */
//#define RESERVED            (0x4000)  /* Comp. E */
//#define RESERVED            (0x8000)  /* Comp. E */

#define CEPWRMD_0              (0x0000)       /* Comp. E Power mode 0 */
#define CEPWRMD_1              (0x0100)       /* Comp. E Power mode 1 */
#define CEPWRMD_2              (0x0200)       /* Comp. E Power mode 2 */
#define CEPWRMD_3              (0x0300)       /* Comp. E Power mode 3*/

#define CEFDLY_0               (0x0000)       /* Comp. E Filter delay 0 : 450ns */
#define CEFDLY_1               (0x0040)       /* Comp. E Filter delay 1 : 900ns */
#define CEFDLY_2               (0x0080)       /* Comp. E Filter delay 2 : 1800ns */
#define CEFDLY_3               (0x00C0)       /* Comp. E Filter delay 3 : 3600ns */

/* CECTL2 Control Bits */
#define CEREF00                (0x0001)       /* Comp. E Reference 0 Resistor Select Bit : 0 */
#define CEREF01                (0x0002)       /* Comp. E Reference 0 Resistor Select Bit : 1 */
#define CEREF02                (0x0004)       /* Comp. E Reference 0 Resistor Select Bit : 2 */
#define CEREF03                (0x0008)       /* Comp. E Reference 0 Resistor Select Bit : 3 */
#define CEREF04                (0x0010)       /* Comp. E Reference 0 Resistor Select Bit : 4 */
#define CERSEL                 (0x0020)       /* Comp. E Reference select */
#define CERS0                  (0x0040)       /* Comp. E Reference Source Bit : 0 */
#define CERS1                  (0x0080)       /* Comp. E Reference Source Bit : 1 */
#define CEREF10                (0x0100)       /* Comp. E Reference 1 Resistor Select Bit : 0 */
#define CEREF11                (0x0200)       /* Comp. E Reference 1 Resistor Select Bit : 1 */
#define CEREF12                (0x0400)       /* Comp. E Reference 1 Resistor Select Bit : 2 */
#define CEREF13                (0x0800)       /* Comp. E Reference 1 Resistor Select Bit : 3 */
#define CEREF14                (0x1000)       /* Comp. E Reference 1 Resistor Select Bit : 4 */
#define CEREFL0                (0x2000)       /* Comp. E Reference voltage level Bit : 0 */
#define CEREFL1                (0x4000)       /* Comp. E Reference voltage level Bit : 1 */
#define CEREFACC               (0x8000)       /* Comp. E Reference Accuracy */

/* CECTL2 Control Bits */
#define CEREF00_L              (0x0001)       /* Comp. E Reference 0 Resistor Select Bit : 0 */
#define CEREF01_L              (0x0002)       /* Comp. E Reference 0 Resistor Select Bit : 1 */
#define CEREF02_L              (0x0004)       /* Comp. E Reference 0 Resistor Select Bit : 2 */
#define CEREF03_L              (0x0008)       /* Comp. E Reference 0 Resistor Select Bit : 3 */
#define CEREF04_L              (0x0010)       /* Comp. E Reference 0 Resistor Select Bit : 4 */
#define CERSEL_L               (0x0020)       /* Comp. E Reference select */
#define CERS0_L                (0x0040)       /* Comp. E Reference Source Bit : 0 */
#define CERS1_L                (0x0080)       /* Comp. E Reference Source Bit : 1 */

/* CECTL2 Control Bits */
#define CEREF10_H              (0x0001)       /* Comp. E Reference 1 Resistor Select Bit : 0 */
#define CEREF11_H              (0x0002)       /* Comp. E Reference 1 Resistor Select Bit : 1 */
#define CEREF12_H              (0x0004)       /* Comp. E Reference 1 Resistor Select Bit : 2 */
#define CEREF13_H              (0x0008)       /* Comp. E Reference 1 Resistor Select Bit : 3 */
#define CEREF14_H              (0x0010)       /* Comp. E Reference 1 Resistor Select Bit : 4 */
#define CEREFL0_H              (0x0020)       /* Comp. E Reference voltage level Bit : 0 */
#define CEREFL1_H              (0x0040)       /* Comp. E Reference voltage level Bit : 1 */
#define CEREFACC_H             (0x0080)       /* Comp. E Reference Accuracy */

#define CEREF0_0               (0x0000)       /* Comp. E Int. Ref.0 Select 0 : 1/32 */
#define CEREF0_1               (0x0001)       /* Comp. E Int. Ref.0 Select 1 : 2/32 */
#define CEREF0_2               (0x0002)       /* Comp. E Int. Ref.0 Select 2 : 3/32 */
#define CEREF0_3               (0x0003)       /* Comp. E Int. Ref.0 Select 3 : 4/32 */
#define CEREF0_4               (0x0004)       /* Comp. E Int. Ref.0 Select 4 : 5/32 */
#define CEREF0_5               (0x0005)       /* Comp. E Int. Ref.0 Select 5 : 6/32 */
#define CEREF0_6               (0x0006)       /* Comp. E Int. Ref.0 Select 6 : 7/32 */
#define CEREF0_7               (0x0007)       /* Comp. E Int. Ref.0 Select 7 : 8/32 */
#define CEREF0_8               (0x0008)       /* Comp. E Int. Ref.0 Select 0 : 9/32 */
#define CEREF0_9               (0x0009)       /* Comp. E Int. Ref.0 Select 1 : 10/32 */
#define CEREF0_10              (0x000A)       /* Comp. E Int. Ref.0 Select 2 : 11/32 */
#define CEREF0_11              (0x000B)       /* Comp. E Int. Ref.0 Select 3 : 12/32 */
#define CEREF0_12              (0x000C)       /* Comp. E Int. Ref.0 Select 4 : 13/32 */
#define CEREF0_13              (0x000D)       /* Comp. E Int. Ref.0 Select 5 : 14/32 */
#define CEREF0_14              (0x000E)       /* Comp. E Int. Ref.0 Select 6 : 15/32 */
#define CEREF0_15              (0x000F)       /* Comp. E Int. Ref.0 Select 7 : 16/32 */
#define CEREF0_16              (0x0010)       /* Comp. E Int. Ref.0 Select 0 : 17/32 */
#define CEREF0_17              (0x0011)       /* Comp. E Int. Ref.0 Select 1 : 18/32 */
#define CEREF0_18              (0x0012)       /* Comp. E Int. Ref.0 Select 2 : 19/32 */
#define CEREF0_19              (0x0013)       /* Comp. E Int. Ref.0 Select 3 : 20/32 */
#define CEREF0_20              (0x0014)       /* Comp. E Int. Ref.0 Select 4 : 21/32 */
#define CEREF0_21              (0x0015)       /* Comp. E Int. Ref.0 Select 5 : 22/32 */
#define CEREF0_22              (0x0016)       /* Comp. E Int. Ref.0 Select 6 : 23/32 */
#define CEREF0_23              (0x0017)       /* Comp. E Int. Ref.0 Select 7 : 24/32 */
#define CEREF0_24              (0x0018)       /* Comp. E Int. Ref.0 Select 0 : 25/32 */
#define CEREF0_25              (0x0019)       /* Comp. E Int. Ref.0 Select 1 : 26/32 */
#define CEREF0_26              (0x001A)       /* Comp. E Int. Ref.0 Select 2 : 27/32 */
#define CEREF0_27              (0x001B)       /* Comp. E Int. Ref.0 Select 3 : 28/32 */
#define CEREF0_28              (0x001C)       /* Comp. E Int. Ref.0 Select 4 : 29/32 */
#define CEREF0_29              (0x001D)       /* Comp. E Int. Ref.0 Select 5 : 30/32 */
#define CEREF0_30              (0x001E)       /* Comp. E Int. Ref.0 Select 6 : 31/32 */
#define CEREF0_31              (0x001F)       /* Comp. E Int. Ref.0 Select 7 : 32/32 */

#define CERS_0                 (0x0000)       /* Comp. E Reference Source 0 : Off */
#define CERS_1                 (0x0040)       /* Comp. E Reference Source 1 : Vcc */
#define CERS_2                 (0x0080)       /* Comp. E Reference Source 2 : Shared Ref. */
#define CERS_3                 (0x00C0)       /* Comp. E Reference Source 3 : Shared Ref. / Off */

#define CEREF1_0               (0x0000)       /* Comp. E Int. Ref.1 Select 0 : 1/32 */
#define CEREF1_1               (0x0100)       /* Comp. E Int. Ref.1 Select 1 : 2/32 */
#define CEREF1_2               (0x0200)       /* Comp. E Int. Ref.1 Select 2 : 3/32 */
#define CEREF1_3               (0x0300)       /* Comp. E Int. Ref.1 Select 3 : 4/32 */
#define CEREF1_4               (0x0400)       /* Comp. E Int. Ref.1 Select 4 : 5/32 */
#define CEREF1_5               (0x0500)       /* Comp. E Int. Ref.1 Select 5 : 6/32 */
#define CEREF1_6               (0x0600)       /* Comp. E Int. Ref.1 Select 6 : 7/32 */
#define CEREF1_7               (0x0700)       /* Comp. E Int. Ref.1 Select 7 : 8/32 */
#define CEREF1_8               (0x0800)       /* Comp. E Int. Ref.1 Select 0 : 9/32 */
#define CEREF1_9               (0x0900)       /* Comp. E Int. Ref.1 Select 1 : 10/32 */
#define CEREF1_10              (0x0A00)       /* Comp. E Int. Ref.1 Select 2 : 11/32 */
#define CEREF1_11              (0x0B00)       /* Comp. E Int. Ref.1 Select 3 : 12/32 */
#define CEREF1_12              (0x0C00)       /* Comp. E Int. Ref.1 Select 4 : 13/32 */
#define CEREF1_13              (0x0D00)       /* Comp. E Int. Ref.1 Select 5 : 14/32 */
#define CEREF1_14              (0x0E00)       /* Comp. E Int. Ref.1 Select 6 : 15/32 */
#define CEREF1_15              (0x0F00)       /* Comp. E Int. Ref.1 Select 7 : 16/32 */
#define CEREF1_16              (0x1000)       /* Comp. E Int. Ref.1 Select 0 : 17/32 */
#define CEREF1_17              (0x1100)       /* Comp. E Int. Ref.1 Select 1 : 18/32 */
#define CEREF1_18              (0x1200)       /* Comp. E Int. Ref.1 Select 2 : 19/32 */
#define CEREF1_19              (0x1300)       /* Comp. E Int. Ref.1 Select 3 : 20/32 */
#define CEREF1_20              (0x1400)       /* Comp. E Int. Ref.1 Select 4 : 21/32 */
#define CEREF1_21              (0x1500)       /* Comp. E Int. Ref.1 Select 5 : 22/32 */
#define CEREF1_22              (0x1600)       /* Comp. E Int. Ref.1 Select 6 : 23/32 */
#define CEREF1_23              (0x1700)       /* Comp. E Int. Ref.1 Select 7 : 24/32 */
#define CEREF1_24              (0x1800)       /* Comp. E Int. Ref.1 Select 0 : 25/32 */
#define CEREF1_25              (0x1900)       /* Comp. E Int. Ref.1 Select 1 : 26/32 */
#define CEREF1_26              (0x1A00)       /* Comp. E Int. Ref.1 Select 2 : 27/32 */
#define CEREF1_27              (0x1B00)       /* Comp. E Int. Ref.1 Select 3 : 28/32 */
#define CEREF1_28              (0x1C00)       /* Comp. E Int. Ref.1 Select 4 : 29/32 */
#define CEREF1_29              (0x1D00)       /* Comp. E Int. Ref.1 Select 5 : 30/32 */
#define CEREF1_30              (0x1E00)       /* Comp. E Int. Ref.1 Select 6 : 31/32 */
#define CEREF1_31              (0x1F00)       /* Comp. E Int. Ref.1 Select 7 : 32/32 */

#define CEREFL_0               (0x0000)       /* Comp. E Reference voltage level 0 : None */
#define CEREFL_1               (0x2000)       /* Comp. E Reference voltage level 1 : 1.2V */
#define CEREFL_2               (0x4000)       /* Comp. E Reference voltage level 2 : 2.0V  */
#define CEREFL_3               (0x6000)       /* Comp. E Reference voltage level 3 : 2.5V  */

#define CEPD0                  (0x0001)       /* Comp. E Disable Input Buffer of Port Register .0 */
#define CEPD1                  (0x0002)       /* Comp. E Disable Input Buffer of Port Register .1 */
#define CEPD2                  (0x0004)       /* Comp. E Disable Input Buffer of Port Register .2 */
#define CEPD3                  (0x0008)       /* Comp. E Disable Input Buffer of Port Register .3 */
#define CEPD4                  (0x0010)       /* Comp. E Disable Input Buffer of Port Register .4 */
#define CEPD5                  (0x0020)       /* Comp. E Disable Input Buffer of Port Register .5 */
#define CEPD6                  (0x0040)       /* Comp. E Disable Input Buffer of Port Register .6 */
#define CEPD7                  (0x0080)       /* Comp. E Disable Input Buffer of Port Register .7 */
#define CEPD8                  (0x0100)       /* Comp. E Disable Input Buffer of Port Register .8 */
#define CEPD9                  (0x0200)       /* Comp. E Disable Input Buffer of Port Register .9 */
#define CEPD10                 (0x0400)       /* Comp. E Disable Input Buffer of Port Register .10 */
#define CEPD11                 (0x0800)       /* Comp. E Disable Input Buffer of Port Register .11 */
#define CEPD12                 (0x1000)       /* Comp. E Disable Input Buffer of Port Register .12 */
#define CEPD13                 (0x2000)       /* Comp. E Disable Input Buffer of Port Register .13 */
#define CEPD14                 (0x4000)       /* Comp. E Disable Input Buffer of Port Register .14 */
#define CEPD15                 (0x8000)       /* Comp. E Disable Input Buffer of Port Register .15 */

#define CEPD0_L                (0x0001)       /* Comp. E Disable Input Buffer of Port Register .0 */
#define CEPD1_L                (0x0002)       /* Comp. E Disable Input Buffer of Port Register .1 */
#define CEPD2_L                (0x0004)       /* Comp. E Disable Input Buffer of Port Register .2 */
#define CEPD3_L                (0x0008)       /* Comp. E Disable Input Buffer of Port Register .3 */
#define CEPD4_L                (0x0010)       /* Comp. E Disable Input Buffer of Port Register .4 */
#define CEPD5_L                (0x0020)       /* Comp. E Disable Input Buffer of Port Register .5 */
#define CEPD6_L                (0x0040)       /* Comp. E Disable Input Buffer of Port Register .6 */
#define CEPD7_L                (0x0080)       /* Comp. E Disable Input Buffer of Port Register .7 */

#define CEPD8_H                (0x0001)       /* Comp. E Disable Input Buffer of Port Register .8 */
#define CEPD9_H                (0x0002)       /* Comp. E Disable Input Buffer of Port Register .9 */
#define CEPD10_H               (0x0004)       /* Comp. E Disable Input Buffer of Port Register .10 */
#define CEPD11_H               (0x0008)       /* Comp. E Disable Input Buffer of Port Register .11 */
#define CEPD12_H               (0x0010)       /* Comp. E Disable Input Buffer of Port Register .12 */
#define CEPD13_H               (0x0020)       /* Comp. E Disable Input Buffer of Port Register .13 */
#define CEPD14_H               (0x0040)       /* Comp. E Disable Input Buffer of Port Register .14 */
#define CEPD15_H               (0x0080)       /* Comp. E Disable Input Buffer of Port Register .15 */

/* CEINT Control Bits */
#define CEIFG                  (0x0001)       /* Comp. E Interrupt Flag */
#define CEIIFG                 (0x0002)       /* Comp. E Interrupt Flag Inverted Polarity */
//#define RESERVED             (0x0004)  /* Comp. E */
//#define RESERVED             (0x0008)  /* Comp. E */
#define CERDYIFG               (0x0010)       /* Comp. E Comparator_E ready interrupt flag */
//#define RESERVED             (0x0020)  /* Comp. E */
//#define RESERVED             (0x0040)  /* Comp. E */
//#define RESERVED             (0x0080)  /* Comp. E */
#define CEIE                   (0x0100)       /* Comp. E Interrupt Enable */
#define CEIIE                  (0x0200)       /* Comp. E Interrupt Enable Inverted Polarity */
//#define RESERVED             (0x0400)  /* Comp. E */
//#define RESERVED             (0x0800)  /* Comp. E */
#define CERDYIE                (0x1000)       /* Comp. E Comparator_E ready interrupt enable */
//#define RESERVED             (0x2000)  /* Comp. E */
//#define RESERVED             (0x4000)  /* Comp. E */
//#define RESERVED             (0x8000)  /* Comp. E */

/* CEINT Control Bits */
#define CEIFG_L                (0x0001)       /* Comp. E Interrupt Flag */
#define CEIIFG_L               (0x0002)       /* Comp. E Interrupt Flag Inverted Polarity */
//#define RESERVED             (0x0004)  /* Comp. E */
//#define RESERVED             (0x0008)  /* Comp. E */
#define CERDYIFG_L             (0x0010)       /* Comp. E Comparator_E ready interrupt flag */
//#define RESERVED             (0x0020)  /* Comp. E */
//#define RESERVED             (0x0040)  /* Comp. E */
//#define RESERVED             (0x0080)  /* Comp. E */
//#define RESERVED             (0x0400)  /* Comp. E */
//#define RESERVED             (0x0800)  /* Comp. E */
//#define RESERVED             (0x2000)  /* Comp. E */
//#define RESERVED             (0x4000)  /* Comp. E */
//#define RESERVED             (0x8000)  /* Comp. E */

/* CEINT Control Bits */
//#define RESERVED             (0x0004)  /* Comp. E */
//#define RESERVED             (0x0008)  /* Comp. E */
//#define RESERVED             (0x0020)  /* Comp. E */
//#define RESERVED             (0x0040)  /* Comp. E */
//#define RESERVED             (0x0080)  /* Comp. E */
#define CEIE_H                 (0x0001)       /* Comp. E Interrupt Enable */
#define CEIIE_H                (0x0002)       /* Comp. E Interrupt Enable Inverted Polarity */
//#define RESERVED             (0x0400)  /* Comp. E */
//#define RESERVED             (0x0800)  /* Comp. E */
#define CERDYIE_H              (0x0010)       /* Comp. E Comparator_E ready interrupt enable */
//#define RESERVED             (0x2000)  /* Comp. E */
//#define RESERVED             (0x4000)  /* Comp. E */
//#define RESERVED             (0x8000)  /* Comp. E */

/* CEIV Definitions */
#define CEIV_NONE              (0x0000)       /* No Interrupt pending */
#define CEIV_CEIFG             (0x0002)       /* CEIFG */
#define CEIV_CEIIFG            (0x0004)       /* CEIIFG */
#define CEIV_CERDYIFG          (0x000A)       /* CERDYIFG */

/*************************************************************
* CRC Module
*************************************************************/
#define __MSP430_HAS_CRC__                    /* Definition to show that Module is available */
#define __MSP430_BASEADDRESS_CRC__ 0x0150
#define CRC_BASE               __MSP430_BASEADDRESS_CRC__

SFR_16BIT(CRCDI);                             /* CRC Data In Register */
SFR_8BIT(CRCDI_L);                            /* CRC Data In Register */
SFR_8BIT(CRCDI_H);                            /* CRC Data In Register */
SFR_16BIT(CRCDIRB);                           /* CRC data in reverse byte Register */
SFR_8BIT(CRCDIRB_L);                          /* CRC data in reverse byte Register */
SFR_8BIT(CRCDIRB_H);                          /* CRC data in reverse byte Register */
SFR_16BIT(CRCINIRES);                         /* CRC Initialisation Register and Result Register */
SFR_8BIT(CRCINIRES_L);                        /* CRC Initialisation Register and Result Register */
SFR_8BIT(CRCINIRES_H);                        /* CRC Initialisation Register and Result Register */
SFR_16BIT(CRCRESR);                           /* CRC reverse result Register */
SFR_8BIT(CRCRESR_L);                          /* CRC reverse result Register */
SFR_8BIT(CRCRESR_H);                          /* CRC reverse result Register */

/*************************************************************
* CRC Module
*************************************************************/
#define __MSP430_HAS_CRC32__                  /* Definition to show that Module is available */
#define __MSP430_BASEADDRESS_CRC32__ 0x0980
#define CRC32_BASE             __MSP430_BASEADDRESS_CRC32__


//sfrl    CRC32DIL0              (0x0980)  /* CRC32 Data In */
SFR_16BIT(CRC32DIW0);                         /* CRC32 Data In */
SFR_8BIT(CRC32DIW0_L);                        /* CRC32 Data In */
SFR_8BIT(CRC32DIW0_H);                        /* CRC32 Data In */
SFR_16BIT(CRC32DIW1);                         /* CRC32 Data In */
SFR_8BIT(CRC32DIW1_L);                        /* CRC32 Data In */
SFR_8BIT(CRC32DIW1_H);                        /* CRC32 Data In */
#define CRC32DIB0              CRC32DIW0_L

//sfrl    CRC32DIRBL0            (0x0984)  /* CRC32 Data In Reversed Bit */
SFR_16BIT(CRC32DIRBW1);                       /* CRC32 Data In Reversed Bit */
SFR_8BIT(CRC32DIRBW1_L);                      /* CRC32 Data In Reversed Bit */
SFR_8BIT(CRC32DIRBW1_H);                      /* CRC32 Data In Reversed Bit */
SFR_16BIT(CRC32DIRBW0);                       /* CRC32 Data In Reversed Bit */
SFR_8BIT(CRC32DIRBW0_L);                      /* CRC32 Data In Reversed Bit */
SFR_8BIT(CRC32DIRBW0_H);                      /* CRC32 Data In Reversed Bit */
#define CRC32DIRBB0            CRC32DIRBW0_H

//sfrl    CRC32INIRESL0          (0x0988)  /* CRC32 Initialization and Result */
SFR_16BIT(CRC32INIRESW0);                     /* CRC32 Initialization and Result */
SFR_8BIT(CRC32INIRESW0_L);                    /* CRC32 Initialization and Result */
SFR_8BIT(CRC32INIRESW0_H);                    /* CRC32 Initialization and Result */
SFR_16BIT(CRC32INIRESW1);                     /* CRC32 Initialization and Result */
SFR_8BIT(CRC32INIRESW1_L);                    /* CRC32 Initialization and Result */
SFR_8BIT(CRC32INIRESW1_H);                    /* CRC32 Initialization and Result */
#define CRC32RESB0             CRC32INIRESW0_L
#define CRC32RESB1             CRC32INIRESW0_H
#define CRC32RESB2             CRC32INIRESW1_L
#define CRC32RESB3             CRC32INIRESW1_H

//sfrl    CRC32RESRL0            (0x098C)  /* CRC32 Result Reverse */
SFR_16BIT(CRC32RESRW1);                       /* CRC32 Result Reverse */
SFR_8BIT(CRC32RESRW1_L);                      /* CRC32 Result Reverse */
SFR_8BIT(CRC32RESRW1_H);                      /* CRC32 Result Reverse */
SFR_16BIT(CRC32RESRW0);                       /* CRC32 Result Reverse */
SFR_8BIT(CRC32RESRW0_L);                      /* CRC32 Result Reverse */
SFR_8BIT(CRC32RESRW0_H);                      /* CRC32 Result Reverse */
#define CRC32RESRB3            CRC32RESRW1_L
#define CRC32RESRB2            CRC32RESRW1_H
#define CRC32RESRB1            CRC32RESRW0_L
#define CRC32RESRB0            CRC32RESRW0_H

//sfrl    CRC16DIL0              (0x0990)  /* CRC16 Data Input */
SFR_16BIT(CRC16DIW0);                         /* CRC16 Data Input */
SFR_8BIT(CRC16DIW0_L);                        /* CRC16 Data Input */
SFR_8BIT(CRC16DIW0_H);                        /* CRC16 Data Input */
SFR_16BIT(CRC16DIW1);                         /* CRC16 Data Input */
SFR_8BIT(CRC16DIW1_L);                        /* CRC16 Data Input */
SFR_8BIT(CRC16DIW1_H);                        /* CRC16 Data Input */
#define CRC16DIB0              CRC16DIW0_L
//sfrl    CRC16DIRBL0            (0x0994)  /* CRC16 Data In Reverse */
SFR_16BIT(CRC16DIRBW1);                       /* CRC16 Data In Reverse */
SFR_8BIT(CRC16DIRBW1_L);                      /* CRC16 Data In Reverse */
SFR_8BIT(CRC16DIRBW1_H);                      /* CRC16 Data In Reverse */
SFR_16BIT(CRC16DIRBW0);                       /* CRC16 Data In Reverse */
SFR_8BIT(CRC16DIRBW0_L);                      /* CRC16 Data In Reverse */
SFR_8BIT(CRC16DIRBW0_H);                      /* CRC16 Data In Reverse */
#define CRC16DIRBB0            CRC16DIRBW0_L

//sfrl    CRC16INIRESL0          (0x0998)  /* CRC16 Init and Result */
SFR_16BIT(CRC16INIRESW0);                     /* CRC16 Init and Result */
SFR_8BIT(CRC16INIRESW0_L);                    /* CRC16 Init and Result */
SFR_8BIT(CRC16INIRESW0_H);                    /* CRC16 Init and Result */
#define CRC16INIRESB1          CRC16INIRESW0_H
#define CRC16INIRESB0          CRC16INIRESW0_L

//sfrl    CRC16RESRL0            (0x099E)  /* CRC16 Result Reverse */
SFR_16BIT(CRC16RESRW0);                       /* CRC16 Result Reverse */
SFR_8BIT(CRC16RESRW0_L);                      /* CRC16 Result Reverse */
SFR_8BIT(CRC16RESRW0_H);                      /* CRC16 Result Reverse */
SFR_16BIT(CRC16RESRW1);                       /* CRC16 Result Reverse */
SFR_8BIT(CRC16RESRW1_L);                      /* CRC16 Result Reverse */
SFR_8BIT(CRC16RESRW1_H);                      /* CRC16 Result Reverse */
#define CRC16RESRB1            CRC16RESRW0_L
#define CRC16RESRB0            CRC16RESRW0_H

/************************************************************
* CLOCK SYSTEM
************************************************************/
#define __MSP430_HAS_CS__                     /* Definition to show that Module is available */
#define __MSP430_BASEADDRESS_CS__ 0x0160
#define CS_BASE                __MSP430_BASEADDRESS_CS__

SFR_16BIT(CSCTL0);                            /* CS Control Register 0 */
SFR_8BIT(CSCTL0_L);                           /* CS Control Register 0 */
SFR_8BIT(CSCTL0_H);                           /* CS Control Register 0 */
SFR_16BIT(CSCTL1);                            /* CS Control Register 1 */
SFR_8BIT(CSCTL1_L);                           /* CS Control Register 1 */
SFR_8BIT(CSCTL1_H);                           /* CS Control Register 1 */
SFR_16BIT(CSCTL2);                            /* CS Control Register 2 */
SFR_8BIT(CSCTL2_L);                           /* CS Control Register 2 */
SFR_8BIT(CSCTL2_H);                           /* CS Control Register 2 */
SFR_16BIT(CSCTL3);                            /* CS Control Register 3 */
SFR_8BIT(CSCTL3_L);                           /* CS Control Register 3 */
SFR_8BIT(CSCTL3_H);                           /* CS Control Register 3 */
SFR_16BIT(CSCTL4);                            /* CS Control Register 4 */
SFR_8BIT(CSCTL4_L);                           /* CS Control Register 4 */
SFR_8BIT(CSCTL4_H);                           /* CS Control Register 4 */
SFR_16BIT(CSCTL5);                            /* CS Control Register 5 */
SFR_8BIT(CSCTL5_L);                           /* CS Control Register 5 */
SFR_8BIT(CSCTL5_H);                           /* CS Control Register 5 */
SFR_16BIT(CSCTL6);                            /* CS Control Register 6 */
SFR_8BIT(CSCTL6_L);                           /* CS Control Register 6 */
SFR_8BIT(CSCTL6_H);                           /* CS Control Register 6 */

/* CSCTL0 Control Bits */

#define CSKEY                  (0xA500)       /* CS Password */
#define CSKEY_H                (0xA5)         /* CS Password for high byte access */

/* CSCTL1 Control Bits */
#define DCOFSEL0               (0x0002)       /* DCO frequency select Bit: 0 */
#define DCOFSEL1               (0x0004)       /* DCO frequency select Bit: 1 */
#define DCOFSEL2               (0x0008)       /* DCO frequency select Bit: 2 */
#define DCORSEL                (0x0040)       /* DCO range select. */

/* CSCTL1 Control Bits */
#define DCOFSEL0_L             (0x0002)       /* DCO frequency select Bit: 0 */
#define DCOFSEL1_L             (0x0004)       /* DCO frequency select Bit: 1 */
#define DCOFSEL2_L             (0x0008)       /* DCO frequency select Bit: 2 */
#define DCORSEL_L              (0x0040)       /* DCO range select. */

#define DCOFSEL_0              (0x0000)       /* DCO frequency select: 0 */
#define DCOFSEL_1              (0x0002)       /* DCO frequency select: 1 */
#define DCOFSEL_2              (0x0004)       /* DCO frequency select: 2 */
#define DCOFSEL_3              (0x0006)       /* DCO frequency select: 3 */
#define DCOFSEL_4              (0x0008)       /* DCO frequency select: 4 */
#define DCOFSEL_5              (0x000A)       /* DCO frequency select: 5 */
#define DCOFSEL_6              (0x000C)       /* DCO frequency select: 6 */
#define DCOFSEL_7              (0x000E)       /* DCO frequency select: 7 */

/* CSCTL2 Control Bits */
#define SELM0                  (0x0001)       /* MCLK Source Select Bit: 0 */
#define SELM1                  (0x0002)       /* MCLK Source Select Bit: 1 */
#define SELM2                  (0x0004)       /* MCLK Source Select Bit: 2 */
//#define RESERVED            (0x0004)    /* RESERVED */
//#define RESERVED            (0x0008)    /* RESERVED */
#define SELS0                  (0x0010)       /* SMCLK Source Select Bit: 0 */
#define SELS1                  (0x0020)       /* SMCLK Source Select Bit: 1 */
#define SELS2                  (0x0040)       /* SMCLK Source Select Bit: 2 */
//#define RESERVED            (0x0040)    /* RESERVED */
//#define RESERVED            (0x0080)    /* RESERVED */
#define SELA0                  (0x0100)       /* ACLK Source Select Bit: 0 */
#define SELA1                  (0x0200)       /* ACLK Source Select Bit: 1 */
#define SELA2                  (0x0400)       /* ACLK Source Select Bit: 2 */
//#define RESERVED            (0x0400)    /* RESERVED */
//#define RESERVED            (0x0800)    /* RESERVED */
//#define RESERVED            (0x1000)    /* RESERVED */
//#define RESERVED            (0x2000)    /* RESERVED */
//#define RESERVED            (0x4000)    /* RESERVED */
//#define RESERVED            (0x8000)    /* RESERVED */

/* CSCTL2 Control Bits */
#define SELM0_L                (0x0001)       /* MCLK Source Select Bit: 0 */
#define SELM1_L                (0x0002)       /* MCLK Source Select Bit: 1 */
#define SELM2_L                (0x0004)       /* MCLK Source Select Bit: 2 */
//#define RESERVED            (0x0004)    /* RESERVED */
//#define RESERVED            (0x0008)    /* RESERVED */
#define SELS0_L                (0x0010)       /* SMCLK Source Select Bit: 0 */
#define SELS1_L                (0x0020)       /* SMCLK Source Select Bit: 1 */
#define SELS2_L                (0x0040)       /* SMCLK Source Select Bit: 2 */
//#define RESERVED            (0x0040)    /* RESERVED */
//#define RESERVED            (0x0080)    /* RESERVED */
//#define RESERVED            (0x0400)    /* RESERVED */
//#define RESERVED            (0x0800)    /* RESERVED */
//#define RESERVED            (0x1000)    /* RESERVED */
//#define RESERVED            (0x2000)    /* RESERVED */
//#define RESERVED            (0x4000)    /* RESERVED */
//#define RESERVED            (0x8000)    /* RESERVED */

/* CSCTL2 Control Bits */
//#define RESERVED            (0x0004)    /* RESERVED */
//#define RESERVED            (0x0008)    /* RESERVED */
//#define RESERVED            (0x0040)    /* RESERVED */
//#define RESERVED            (0x0080)    /* RESERVED */
#define SELA0_H                (0x0001)       /* ACLK Source Select Bit: 0 */
#define SELA1_H                (0x0002)       /* ACLK Source Select Bit: 1 */
#define SELA2_H                (0x0004)       /* ACLK Source Select Bit: 2 */
//#define RESERVED            (0x0400)    /* RESERVED */
//#define RESERVED            (0x0800)    /* RESERVED */
//#define RESERVED            (0x1000)    /* RESERVED */
//#define RESERVED            (0x2000)    /* RESERVED */
//#define RESERVED            (0x4000)    /* RESERVED */
//#define RESERVED            (0x8000)    /* RESERVED */

#define SELM_0                 (0x0000)       /* MCLK Source Select 0 */
#define SELM_1                 (0x0001)       /* MCLK Source Select 1 */
#define SELM_2                 (0x0002)       /* MCLK Source Select 2 */
#define SELM_3                 (0x0003)       /* MCLK Source Select 3 */
#define SELM_4                 (0x0004)       /* MCLK Source Select 4 */
#define SELM_5                 (0x0005)       /* MCLK Source Select 5 */
#define SELM_6                 (0x0006)       /* MCLK Source Select 6 */
#define SELM_7                 (0x0007)       /* MCLK Source Select 7 */
#define SELM__LFXTCLK          (0x0000)       /* MCLK Source Select LFXTCLK */
#define SELM__VLOCLK           (0x0001)       /* MCLK Source Select VLOCLK */
#define SELM__LFMODCLK         (0x0002)       /* MCLK Source Select LFMODOSC */
#define SELM__LFMODOSC         (0x0002)       /* MCLK Source Select LFMODOSC (legacy) */
#define SELM__DCOCLK           (0x0003)       /* MCLK Source Select DCOCLK */
#define SELM__MODCLK           (0x0004)       /* MCLK Source Select MODOSC */
#define SELM__MODOSC           (0x0004)       /* MCLK Source Select MODOSC (legacy) */
#define SELM__HFXTCLK          (0x0005)       /* MCLK Source Select HFXTCLK */

#define SELS_0                 (0x0000)       /* SMCLK Source Select 0 */
#define SELS_1                 (0x0010)       /* SMCLK Source Select 1 */
#define SELS_2                 (0x0020)       /* SMCLK Source Select 2 */
#define SELS_3                 (0x0030)       /* SMCLK Source Select 3 */
#define SELS_4                 (0x0040)       /* SMCLK Source Select 4 */
#define SELS_5                 (0x0050)       /* SMCLK Source Select 5 */
#define SELS_6                 (0x0060)       /* SMCLK Source Select 6 */
#define SELS_7                 (0x0070)       /* SMCLK Source Select 7 */
#define SELS__LFXTCLK          (0x0000)       /* SMCLK Source Select LFXTCLK */
#define SELS__VLOCLK           (0x0010)       /* SMCLK Source Select VLOCLK */
#define SELS__LFMODCLK         (0x0020)       /* SMCLK Source Select LFMODOSC */
#define SELS__LFMODOSC         (0x0020)       /* SMCLK Source Select LFMODOSC (legacy) */
#define SELS__DCOCLK           (0x0030)       /* SMCLK Source Select DCOCLK */
#define SELS__MODCLK           (0x0040)       /* SMCLK Source Select MODOSC */
#define SELS__MODOSC           (0x0040)       /* SMCLK Source Select MODOSC (legacy) */
#define SELS__HFXTCLK          (0x0050)       /* SMCLK Source Select HFXTCLK */
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
